ceteras/CoBra/adapter/s-video/images/20240106_163255.jpg

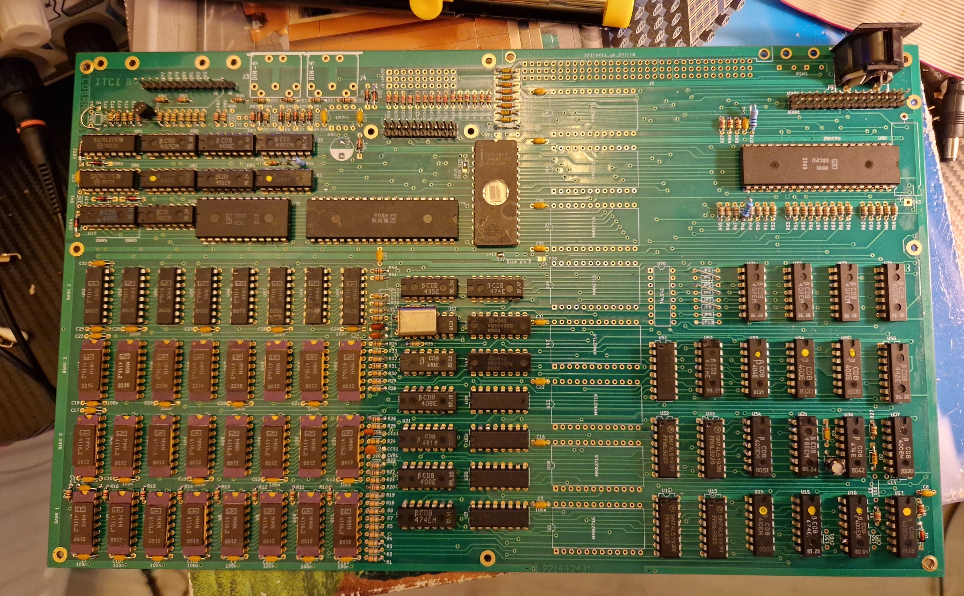
adapter/s-video/images/20240106_163255.jpg
