ceteras/CoBra/adapter/USB-Keyboard/images/20240617_141832.jpg

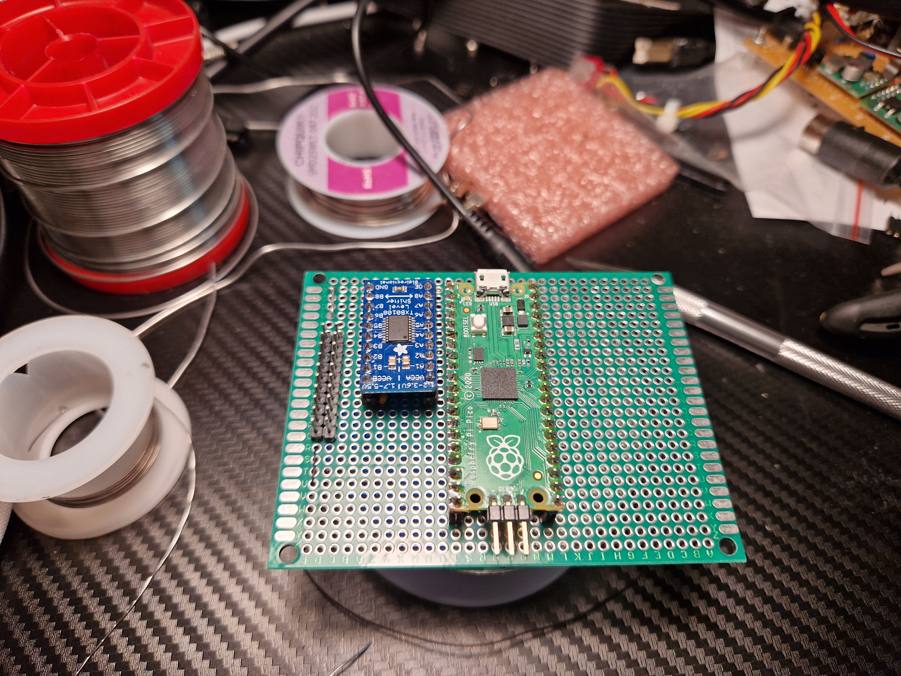
adapter/USB-Keyboard/images/20240617_141832.jpg
