ceteras/CoBra/mainboard/2layer/kicad/main.png

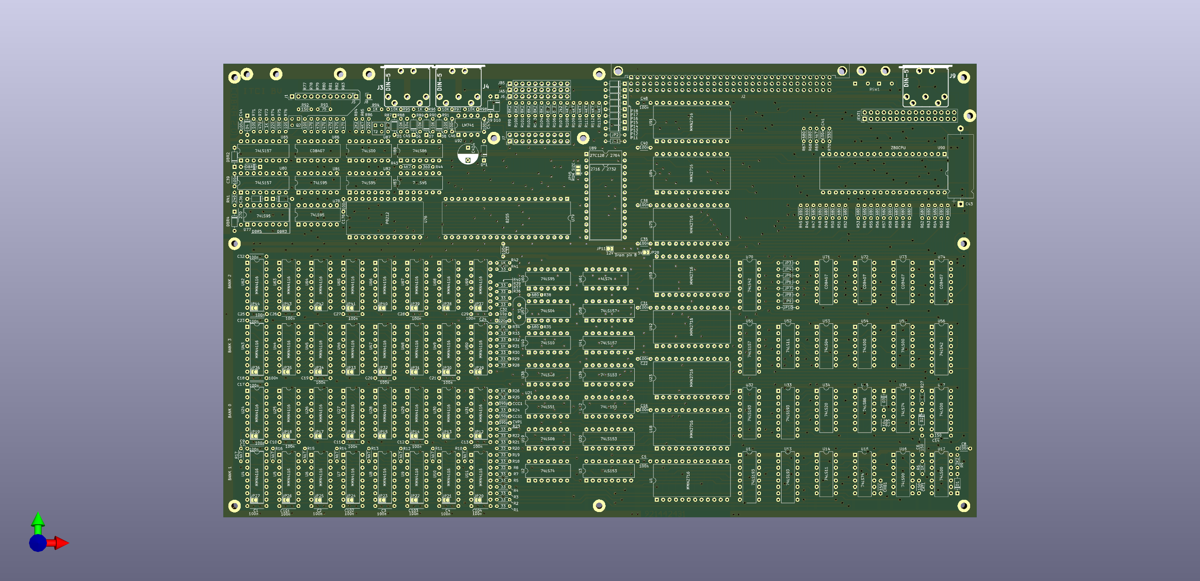
mainboard/2layer/kicad/main.png
