ceteras/CoBra/mainboard/2layer/kicad/Interface.kicad_sch

## KiCad design mainboard/2layer/kicad/Interface.kicad_sch (2023-11-16)

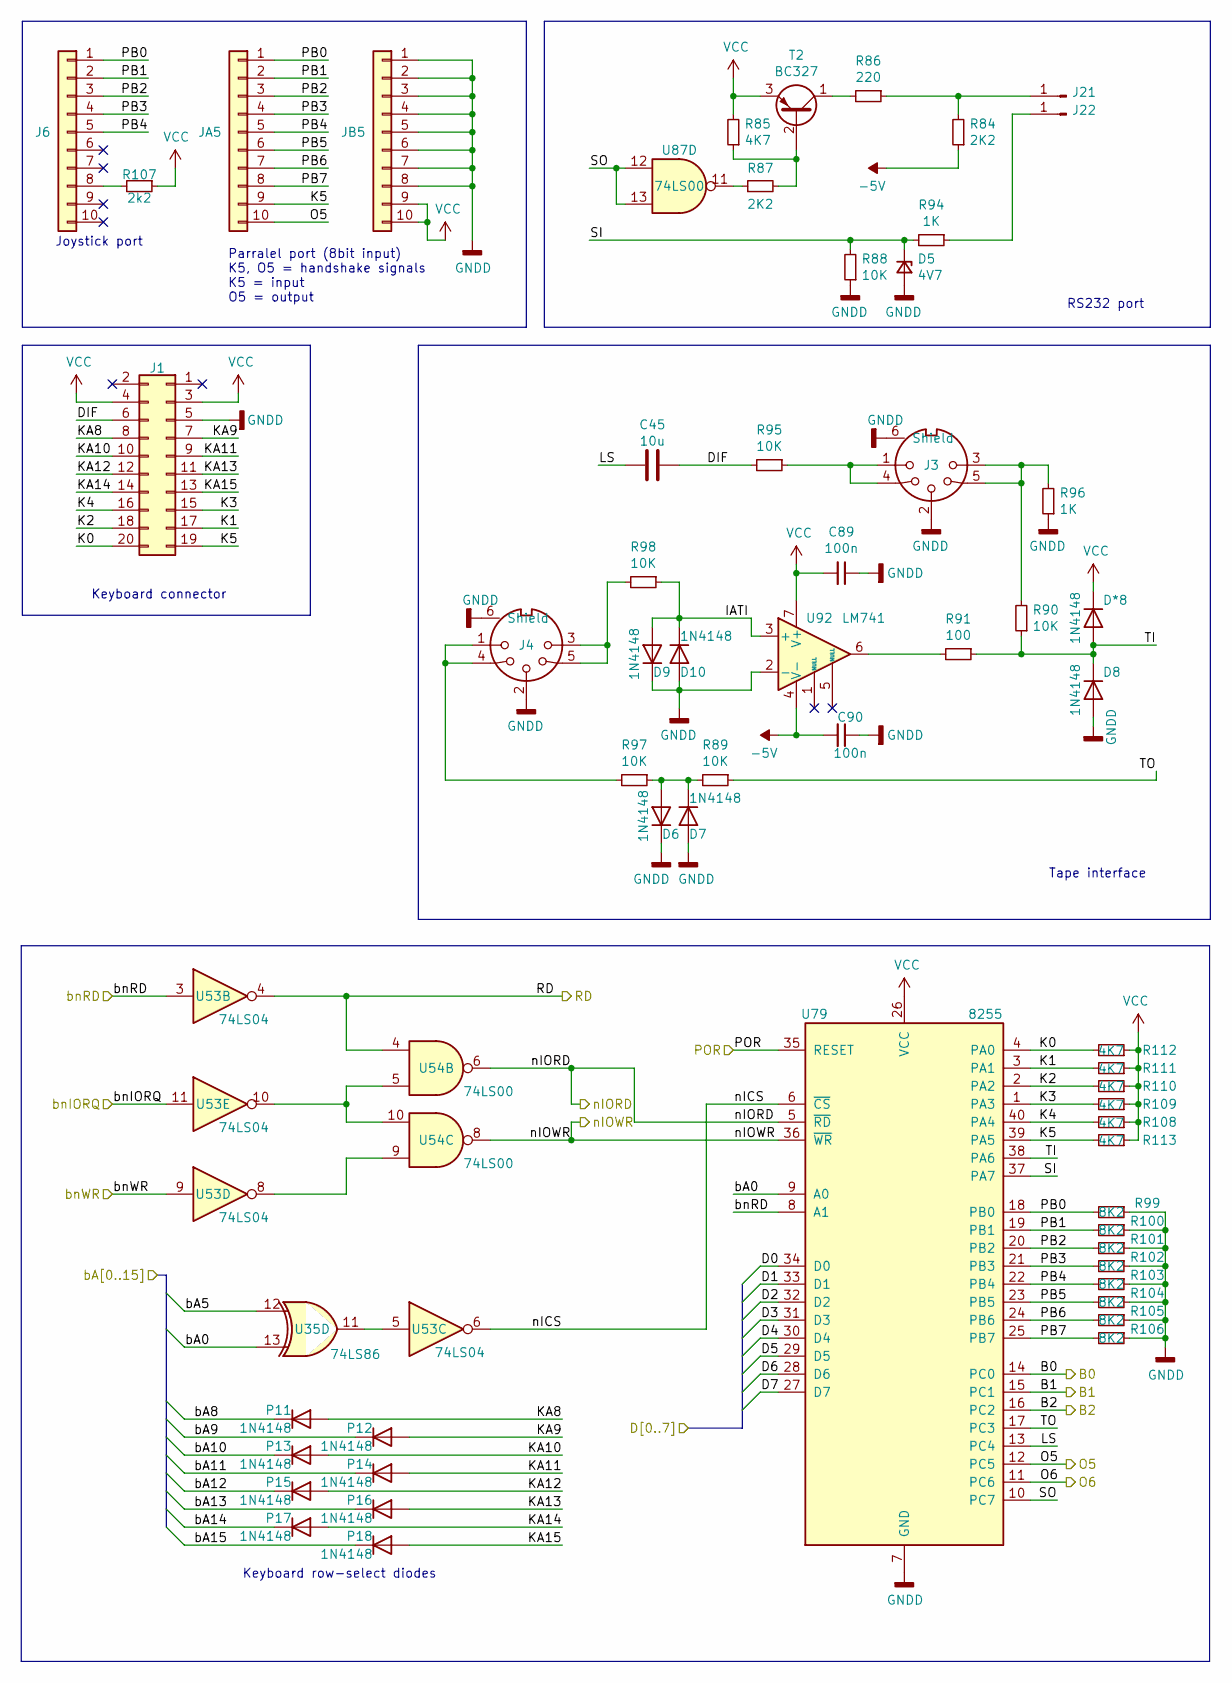
[picture p32: schematic Interface.kicad_sch]

Parts:
C45: 10u; C_THT_508_254
C89, C90: 100n; C_THT_508_254
D5: 4V7; D_DO-35_SOD27_P7.62mm_Horizontal
D6, D7, D8, D9, D10: 1N4148; D_DO-35_SOD27_P7.62mm_Horizontal
D*8: 1N4148; D_DO-35_SOD27_P7.62mm_Horizontal
J1: Conn_02x10_Odd_Even_MountingPin; PinHeader_2x10_P2.54mm_Vertical
J3, J4: DIN-5
J6: Conn_01x10; PinHeader_1x10_P2.54mm_Vertical
J21, J22: Conn_01x01_Male; PinHeader_1x01_P2.54mm_Vertical
JA5: Conn_01x10; PinHeader_1x10_P2.54mm_Vertical
JB5: Conn_01x10; PinHeader_1x10_P2.54mm_Vertical
P11, P12, P13, P14, P15, P16, P17, P18: 1N4148; D_DO-35_SOD27_P7.62mm_Horizontal
R84, R87: 2K2; R_Axial_DIN0204_L3.6mm_D1.6mm_P5.08mm_Horizontal
R85, R108, R109, R110, R111, R112, R113: 4K7; R_Axial_DIN0204_L3.6mm_D1.6mm_P5.08mm_Horizontal
R86: 220; R_Axial_DIN0204_L3.6mm_D1.6mm_P5.08mm_Horizontal
R88, R89, R90, R95, R97, R98: 10K; R_Axial_DIN0204_L3.6mm_D1.6mm_P5.08mm_Horizontal
R91: 100; R_Axial_DIN0204_L3.6mm_D1.6mm_P5.08mm_Horizontal
R94, R96: 1K; R_Axial_DIN0204_L3.6mm_D1.6mm_P5.08mm_Horizontal
R99, R100, R101, R102, R103, R104, R105, R106: 8K2; R_Axial_DIN0204_L3.6mm_D1.6mm_P5.08mm_Horizontal
R107: 2k2; R_Axial_DIN0204_L3.6mm_D1.6mm_P5.08mm_Horizontal
T2: BC327; TO-92-CobraRev
U35: 74LS86; DIP-14_W7.62mm
U53: 74LS04; DIP-14_W7.62mm
U54, U87: 74LS00; DIP-14_W7.62mm
U79: 8255; DIP-40_W15.24mm
U92: LM741; DIP-8_W7.62mm

Connections:
-5V: C90.2, R84.1, U92.4 (V-)
B0: U79.14 (PC0)
B1: U79.15 (PC1)
B2: U79.16 (PC2)
D0: U79.34 (D0)
D1: U79.33 (D1)
D2: U79.32 (D2)
D3: U79.31 (D3)
D4: U79.30 (D4)
D5: U79.29 (D5)
D6: U79.28 (D6)
D7: U79.27 (D7)
DIF: C45.2, J1.6, R95.2
GNDD: C89.1, C90.1, D5.2 (A), D6.1 (K), D7.2 (A), D8.2 (A), D9.1 (K), D10.2 (A), J1.5, J3.2, J3.6 (Shield), J4.2, J4.6 (Shield), JB5.1, JB5.2, JB5.3, JB5.4, JB5.5, JB5.6, JB5.7, JB5.8, R88.1, R96.1, R99.1, R100.1, R101.1, R102.1, R103.1, R104.1, R105.1, R106.1, U79.7 (GND), U92.2 (-)
IATI: D9.2 (A), D10.1 (K), R98.1, U92.3 (+)
K0: J1.20, R112.2, U79.4 (PA0)
K1: J1.17, R111.2, U79.3 (PA1)
K2: J1.18, R110.2, U79.2 (PA2)
K3: J1.15, R109.2, U79.1 (PA3)
K4: J1.16, R108.2, U79.40 (PA4)
K5: J1.19, JA5.9, R113.2, U79.39 (PA5)
KA8: J1.8, P11.2 (A)
KA9: J1.7, P12.2 (A)
KA10: J1.10, P13.2 (A)
KA11: J1.9, P14.2 (A)
KA12: J1.12, P15.2 (A)
KA13: J1.11, P16.2 (A)
KA14: J1.14, P17.2 (A)
KA15: J1.13, P18.2 (A)
LS: C45.1, U79.13 (PC4)
unnamed: D6.2 (A), D7.1 (K), R89.2, R97.1
unnamed: J3.1, J3.4, R95.1
unnamed: J3.3, J3.5, R90.2, R96.2
unnamed: J4.1, J4.4, R97.2
unnamed: J4.3, J4.5, R98.2
unnamed: J6.8, R107.2
unnamed: J21.1, R84.2, R86.1
unnamed: J22.1, R94.1
unnamed: R85.1, R87.2, T2.2 (B)
unnamed: R86.2, T2.1 (C)
unnamed: R87.1, U87.11
unnamed: R91.2, U92.6
unnamed: U35.11, U53.5
unnamed: U53.8, U54.9
unnamed: U53.10, U54.5, U54.10
O5: JA5.10, U79.12 (PC5)
O6: U79.11 (PC6)
PB0: J6.1, JA5.1, R99.2, U79.18 (PB0)
PB1: J6.2, JA5.2, R100.2, U79.19 (PB1)
PB2: J6.3, JA5.3, R101.2, U79.20 (PB2)
PB3: J6.4, JA5.4, R102.2, U79.21 (PB3)
PB4: J6.5, JA5.5, R103.2, U79.22 (PB4)
PB5: JA5.6, R104.2, U79.23 (PB5)
PB6: JA5.7, R105.2, U79.24 (PB6)
PB7: JA5.8, R106.2, U79.25 (PB7)
POR: U79.35 (RESET)
RD: U53.4, U54.4
SI: D5.1 (K), R88.2, R94.2, U79.37 (PA7)
SO: U79.10 (PC7), U87.12, U87.13
TI: D8.1 (K), D*8.2 (A), R90.1, R91.1, U79.38 (PA6)
TO: R89.1, U79.17 (PC3)
VCC: C89.2, D*8.1 (K), J1.3, J1.4, JB5.9, JB5.10, R85.2, R107.1, R108.1, R109.1, R110.1, R111.1, R112.1, R113.1, T2.3 (E), U79.26 (VCC), U92.7 (V+)
bA0: U35.13, U79.9 (A0)
bA5: U35.12
bA8: P11.1 (K)
bA9: P12.1 (K)
bA10: P13.1 (K)
bA11: P14.1 (K)
bA12: P15.1 (K)
bA13: P16.1 (K)
bA14: P17.1 (K)
bA15: P18.1 (K)
bnIORQ: U53.11
bnRD: U53.3, U79.8 (A1)
bnWR: U53.9
nICS: U53.6, U79.6 (~CS)
nIORD: U54.6, U79.5 (~RD)
nIOWR: U54.8, U79.36 (~WR)

Notes on the sheet:
Tape interface
Keyboard connector
Keyboard row-select diodes
Joystick port
RS232 port
Parralel port (8bit input) K5, O5 = handshake signals K5 = input O5 = output
