ceteras/CoBra/mainboard/2layer/kicad/Memory_arbiter_cmd.kicad_sch

## KiCad design mainboard/2layer/kicad/Memory_arbiter_cmd.kicad_sch (2023-11-17)

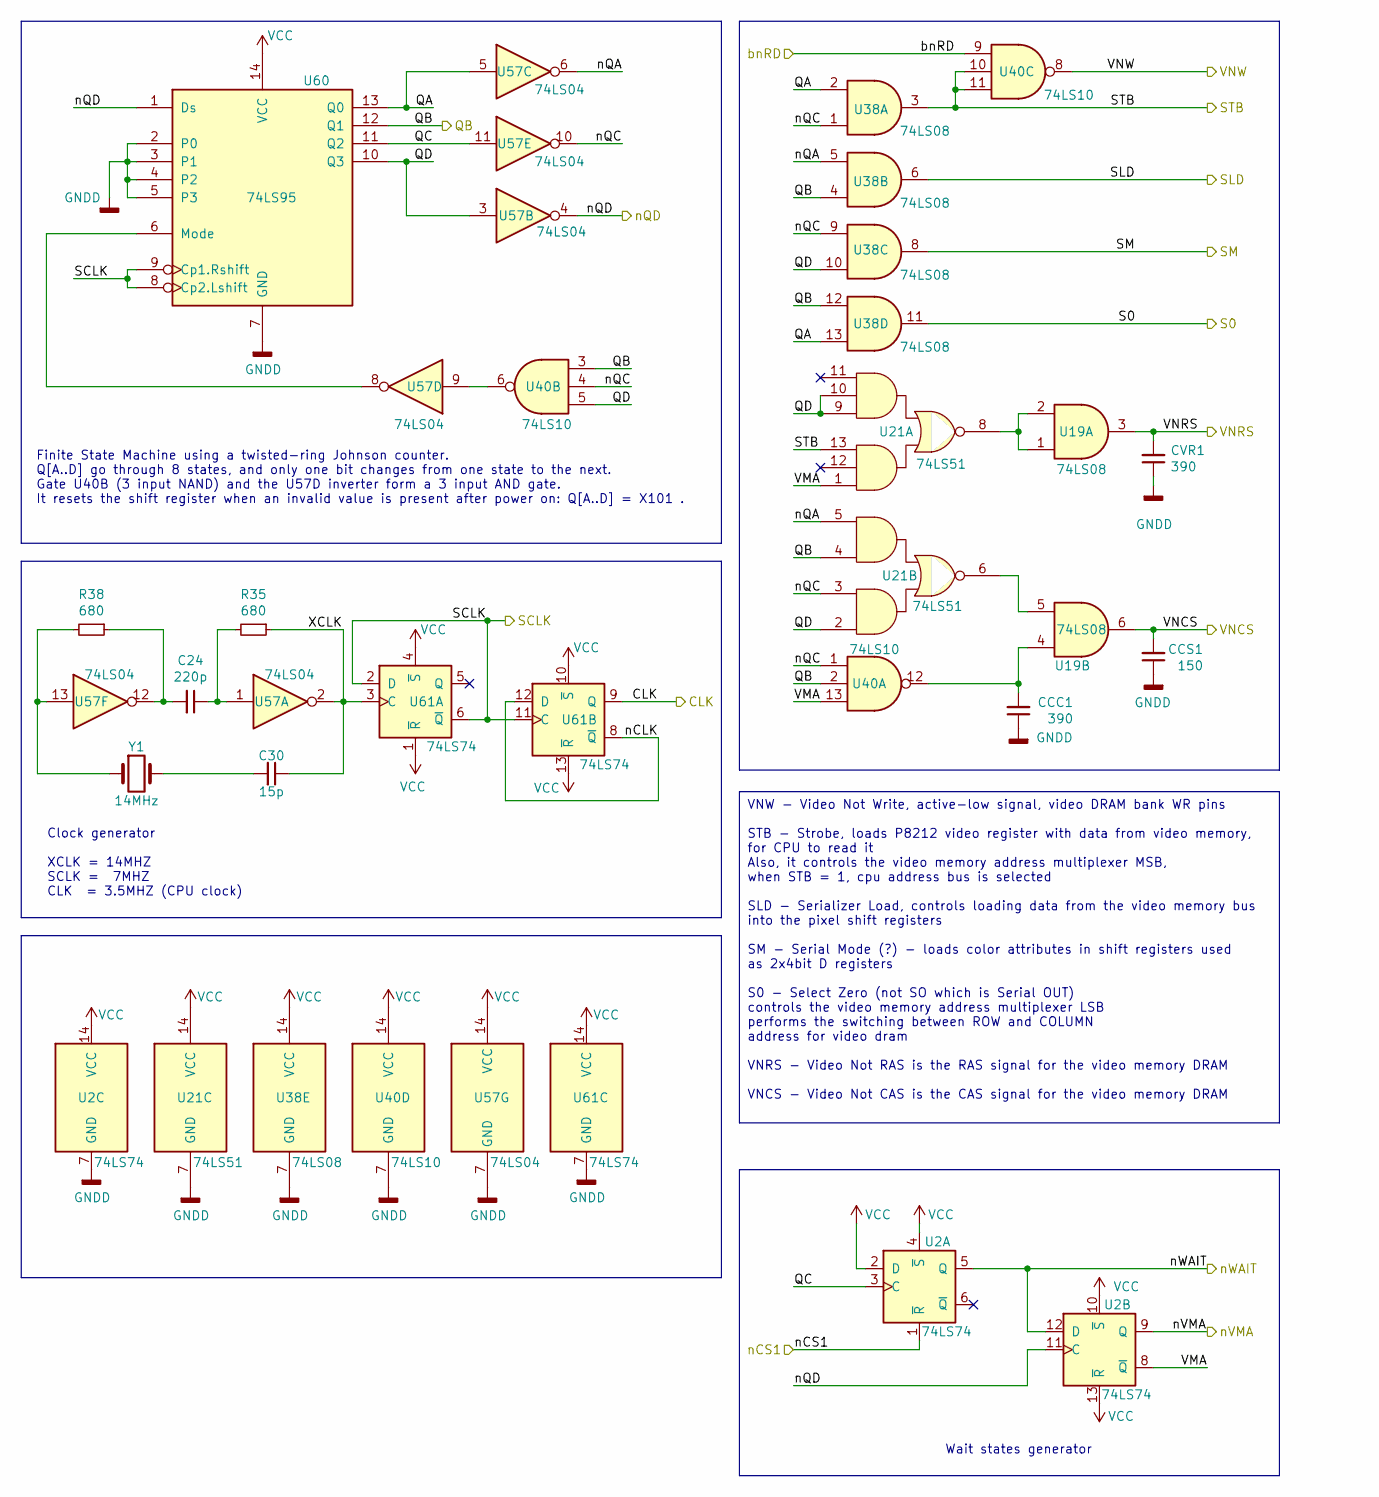
[picture p33: schematic Memory_arbiter_cmd.kicad_sch]

Parts:
C24: 220p; C_THT_508_254
C30: 15p; C_THT_508_254
CCC1: 390; C_THT_508_254
CCS1: 150; C_THT_508_254
CVR1: 390; C_THT_508_254
R35, R38: 680; R_Axial_DIN0204_L3.6mm_D1.6mm_P5.08mm_Horizontal
U2, U61: 74LS74; DIP-14_W7.62mm
U19, U38: 74LS08; DIP-14_W7.62mm
U21: 74LS51; DIP-14_W7.62mm
U40: 74LS10; DIP-14_W7.62mm
U57: 74LS04; DIP-14_W7.62mm
U60: 74LS95; DIP-14_W7.62mm
Y1: 14MHz; Crystal_HC18-U_Vertical

Connections:
CLK: U61.9 (Q)
GNDD: CCC1.1, CCS1.1, CVR1.1, U2.7 (GND), U21.7 (GND), U38.7 (GND), U40.7 (GND), U57.7 (GND), U60.2 (P0), U60.3 (P1), U60.4 (P2), U60.5 (P3), U60.7 (GND), U61.7 (GND)
unnamed: C24.1, R35.2, U57.1
unnamed: C24.2, R38.1, U57.12
unnamed: C30.2, Y1.2
unnamed: CCC1.2, U19.4, U40.12
unnamed: R38.2, U57.13, Y1.1
unnamed: U19.1, U19.2, U21.8
unnamed: U19.5, U21.6
unnamed: U40.6, U57.9
unnamed: U57.8, U60.6 (Mode)
QA: U38.2, U38.13, U57.5, U60.13 (Q0)
QB: U21.4, U38.4, U38.12, U40.2, U40.3, U60.12 (Q1)
QC: U2.3 (C), U57.11, U60.11 (Q2)
QD: U21.2, U21.9, U21.10, U38.10, U40.5, U57.3, U60.10 (Q3)
S0: U38.11
SCLK: U60.8 (Cp2.Lshift), U60.9 (Cp1.Rshift), U61.2 (D), U61.6 (~Q), U61.11 (C)
SLD: U38.6
SM: U38.8
STB: U21.13, U38.3, U40.10, U40.11
VCC: U2.2 (D), U2.4 (~S), U2.10 (~S), U2.13 (~R), U2.14 (VCC), U21.14 (VCC), U38.14 (VCC), U40.14 (VCC), U57.14 (VCC), U60.14 (VCC), U61.1 (~R), U61.4 (~S), U61.10 (~S), U61.13 (~R), U61.14 (VCC)
VMA: U2.8 (~Q), U21.1, U40.13
VNCS: CCS1.2, U19.6
VNRS: CVR1.2, U19.3
VNW: U40.8
XCLK: C30.1, R35.1, U57.2, U61.3 (C)
bnRD: U40.9
nCLK: U61.8 (~Q), U61.12 (D)
nCS1: U2.1 (~R)
nQA: U21.5, U38.5, U57.6
nQC: U21.3, U38.1, U38.9, U40.1, U40.4, U57.10
nQD: U2.11 (C), U57.4, U60.1 (Ds)
nVMA: U2.9 (Q)
nWAIT: U2.5 (Q), U2.12 (D)

Notes on the sheet:
VNW - Video Not Write, active-low signal, video DRAM bank WR pins STB - Strobe, loads P8212 video register with data from video memory, for CPU to read it Also, it controls the video memory address multiplexer MSB, when STB = 1, cpu address bus is selected SLD - Serializer Load, controls loading da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
Wait states generator
Clock generator XCLK = 14MHZ SCLK = 7MHZ CLK = 3.5MHZ (CPU clock)
Finite State Machine using a twisted-ring Johnson counter. Q[A..D] go through 8 states, and only one bit changes from one state to the next. Gate U40B (3 input NAND) and the U57D inverter form a 3 input AND gate. It resets the shift register when an invalid value is present after power on: Q[A..D] 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
