ceteras/CoBra/mainboard/2layer/kicad/Mux_video_address.kicad_sch

## KiCad design mainboard/2layer/kicad/Mux_video_address.kicad_sch (2023-11-15)

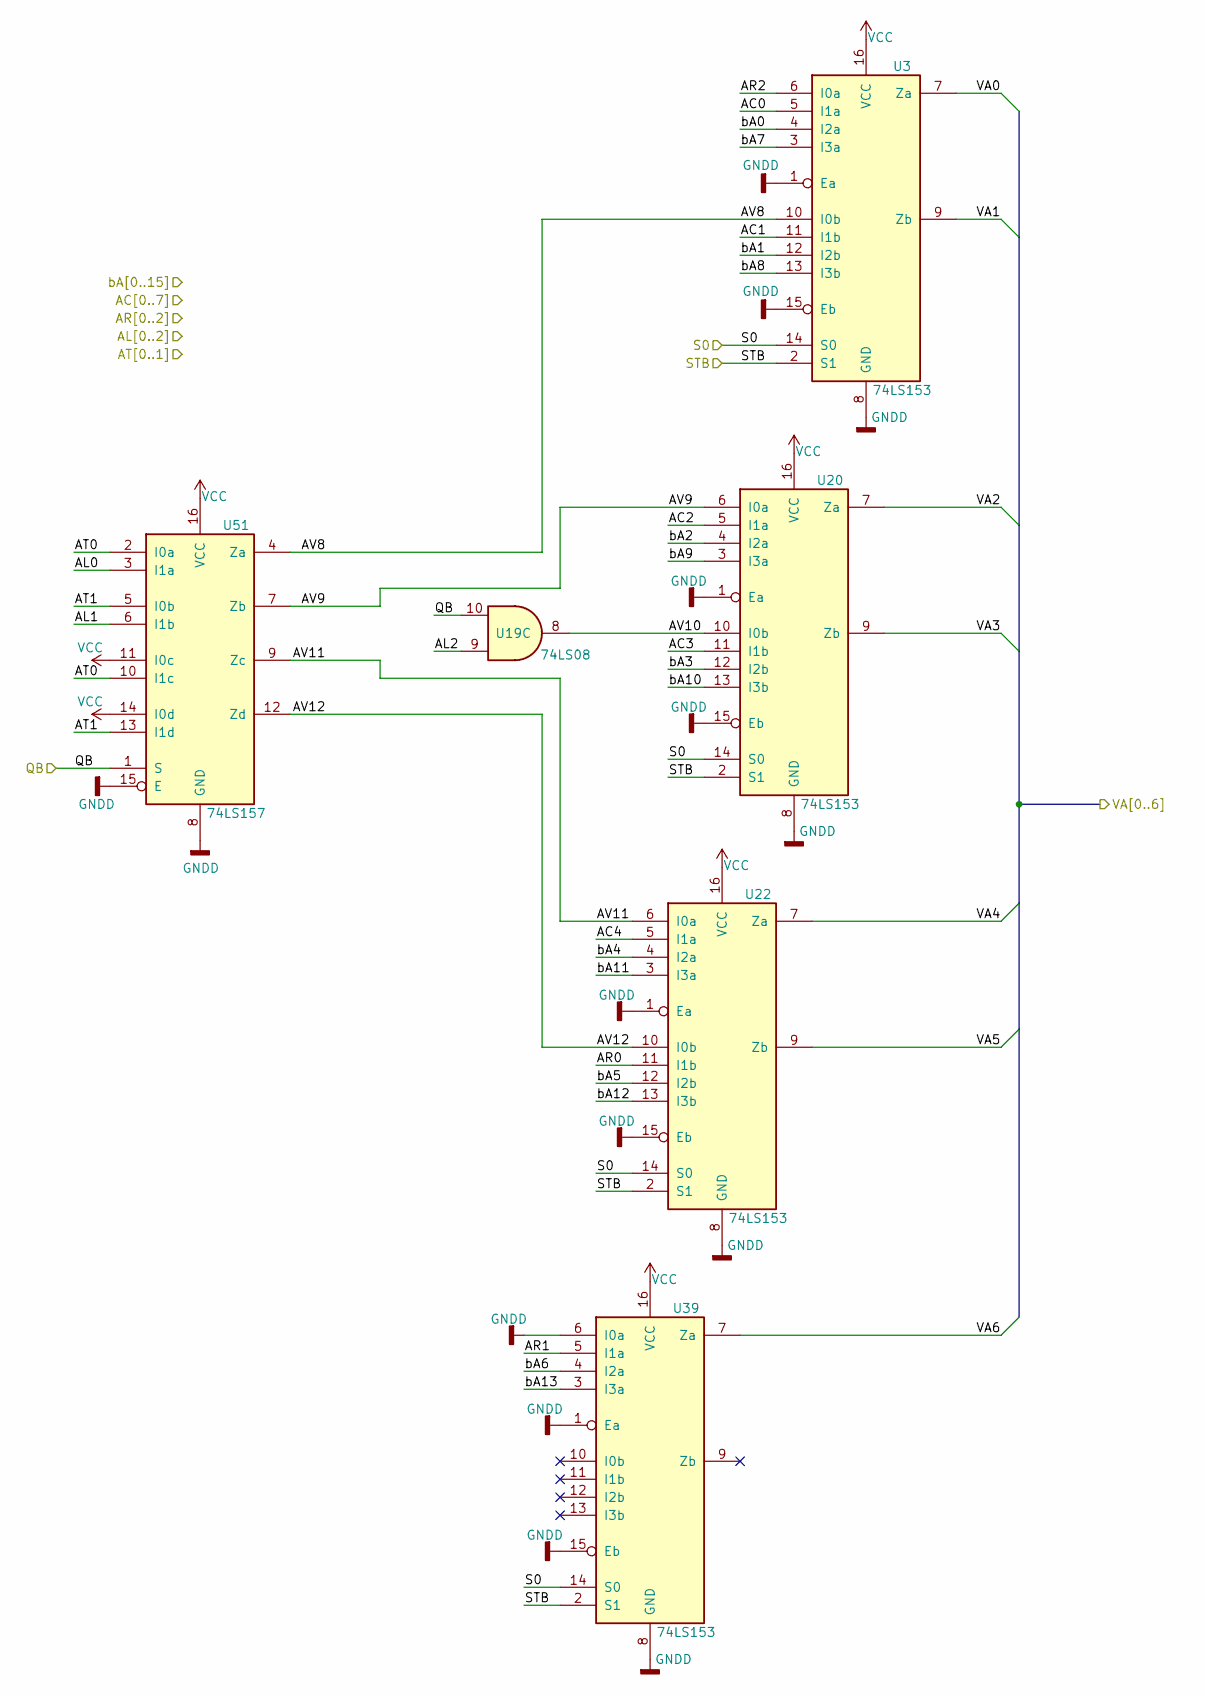
[picture p34: schematic Mux_video_address.kicad_sch]

Parts:
U3, U20, U22, U39: 74LS153; DIP-16_W7.62mm
U19: 74LS08; DIP-14_W7.62mm
U51: 74LS157; DIP-16_W7.62mm

Connections:
AC0: U3.5 (I1a)
AC1: U3.11 (I1b)
AC2: U20.5 (I1a)
AC3: U20.11 (I1b)
AC4: U22.5 (I1a)
AL0: U51.3 (I1a)
AL1: U51.6 (I1b)
AL2: U19.9
AR0: U22.11 (I1b)
AR1: U39.5 (I1a)
AR2: U3.6 (I0a)
AT0: U51.2 (I0a), U51.10 (I1c)
AT1: U51.5 (I0b), U51.13 (I1d)
AV8: U3.10 (I0b), U51.4 (Za)
AV9: U20.6 (I0a), U51.7 (Zb)
AV10: U19.8, U20.10 (I0b)
AV11: U22.6 (I0a), U51.9 (Zc)
AV12: U22.10 (I0b), U51.12 (Zd)
GNDD: U3.1 (Ea), U3.8 (GND), U3.15 (Eb), U20.1 (Ea), U20.8 (GND), U20.15 (Eb), U22.1 (Ea), U22.8 (GND), U22.15 (Eb), U39.1 (Ea), U39.6 (I0a), U39.8 (GND), U39.15 (Eb), U51.8 (GND), U51.15 (E)
QB: U19.10, U51.1 (S)
S0: U3.14 (S0), U20.14 (S0), U22.14 (S0), U39.14 (S0)
STB: U3.2 (S1), U20.2 (S1), U22.2 (S1), U39.2 (S1)
VA0: U3.7 (Za)
VA1: U3.9 (Zb)
VA2: U20.7 (Za)
VA3: U20.9 (Zb)
VA4: U22.7 (Za)
VA5: U22.9 (Zb)
VA6: U39.7 (Za)
VCC: U3.16 (VCC), U20.16 (VCC), U22.16 (VCC), U39.16 (VCC), U51.11 (I0c), U51.14 (I0d), U51.16 (VCC)
bA0: U3.4 (I2a)
bA1: U3.12 (I2b)
bA2: U20.4 (I2a)
bA3: U20.12 (I2b)
bA4: U22.4 (I2a)
bA5: U22.12 (I2b)
bA6: U39.4 (I2a)
bA7: U3.3 (I3a)
bA8: U3.13 (I3b)
bA9: U20.3 (I3a)
bA10: U20.13 (I3b)
bA11: U22.3 (I3a)
bA12: U22.13 (I3b)
bA13: U39.3 (I3a)
