ceteras/CoBra/mainboard/2layer/kicad/RAM_48.kicad_sch

## KiCad design mainboard/2layer/kicad/RAM_48.kicad_sch (2023-11-16)

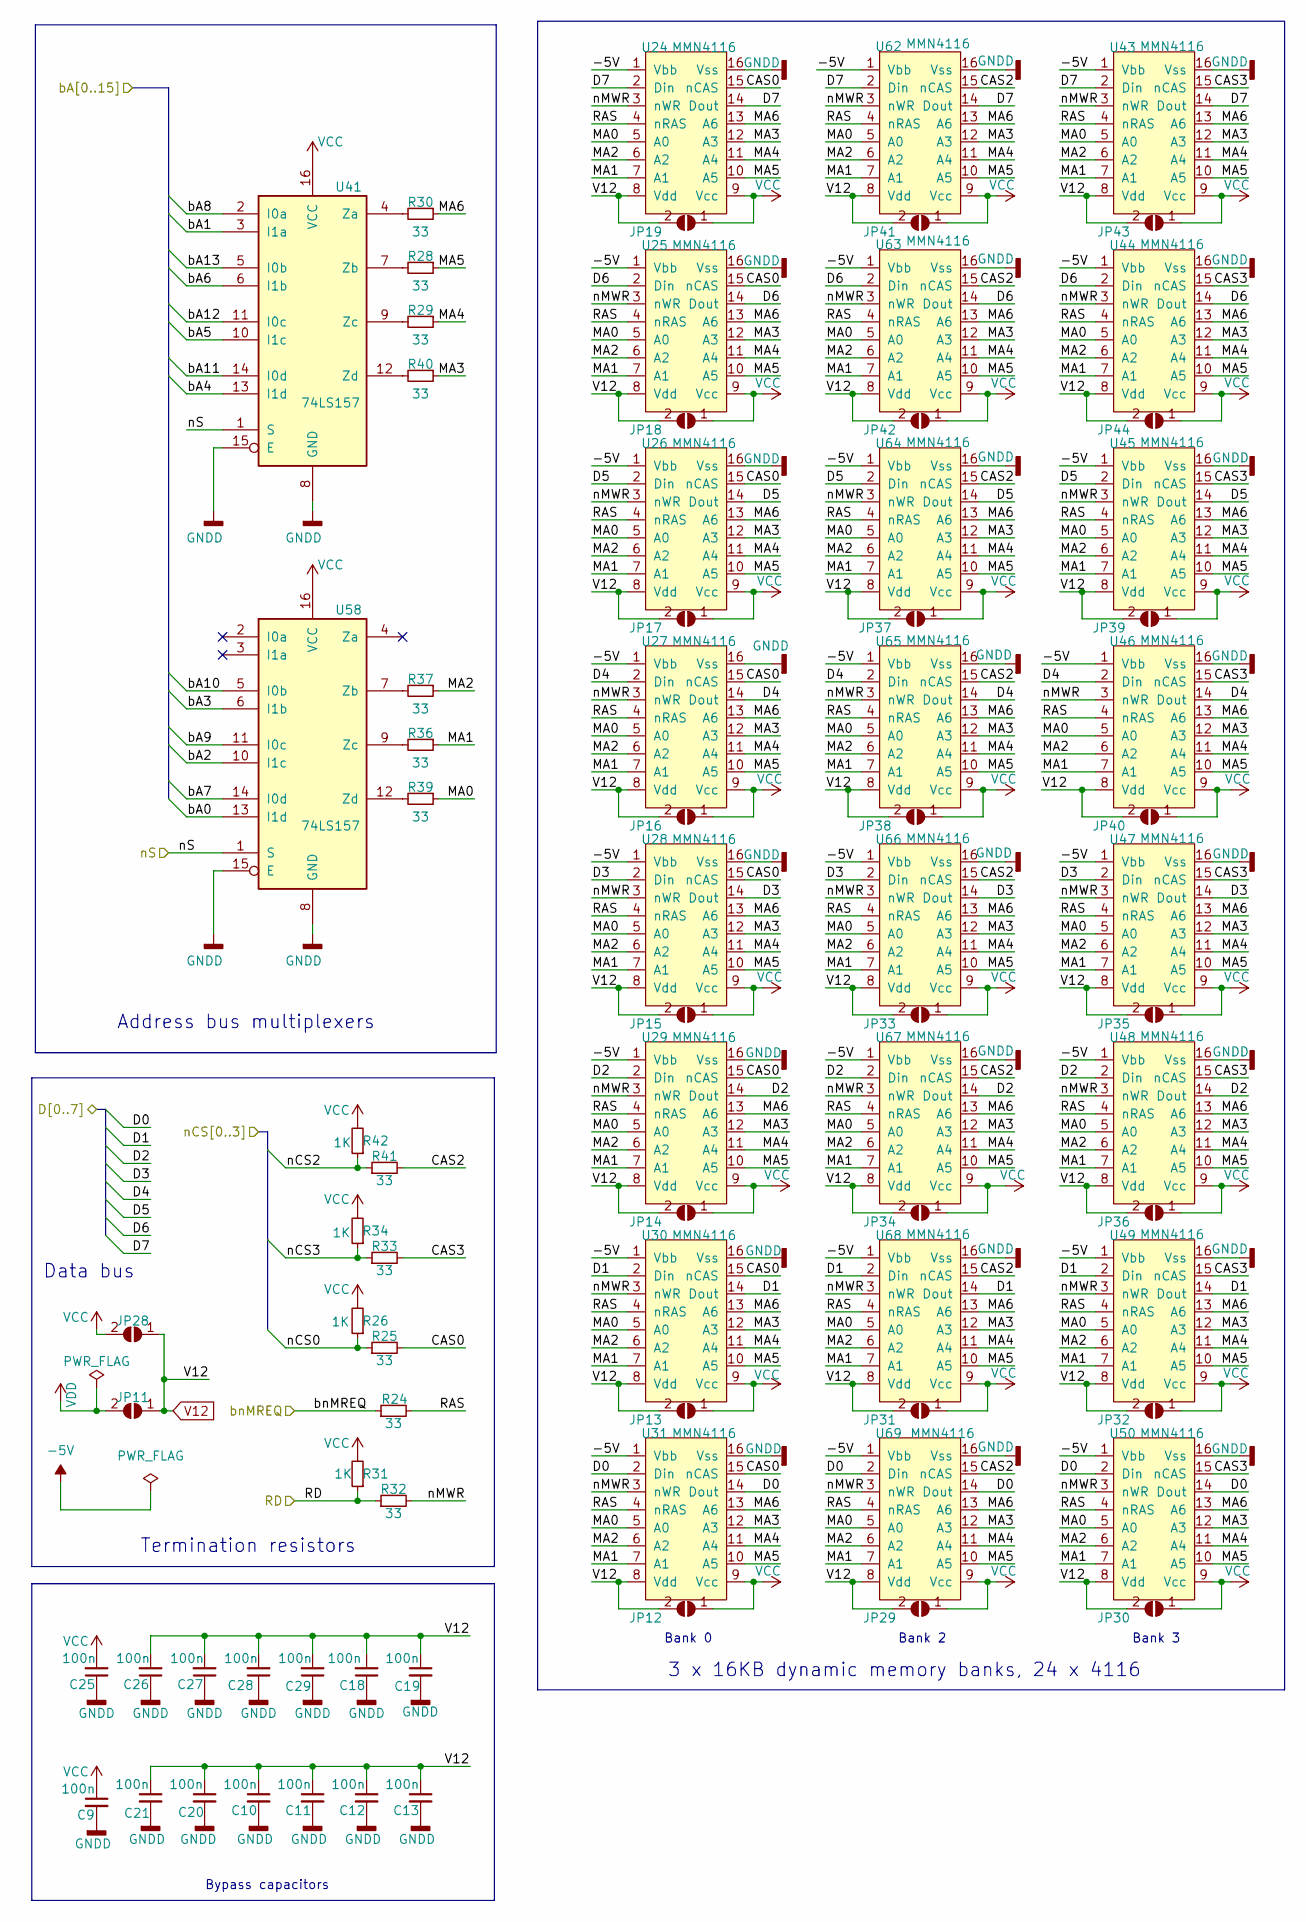
[picture p35: schematic RAM_48.kicad_sch]

Parts:
C9, C10, C11, C12, C13, C18, C19, C20, C21, C25, C26, C27, C28, C29: 100n; C_THT_762_254
JP11, JP12, JP13, JP14, JP15, JP16, JP17, JP18, JP19, JP28, JP29, JP30, JP31, JP32, JP33, JP34, JP35, JP36, JP37, JP38, JP39, JP40, JP41, JP42, JP43, JP44: SolderJumper_2_Open; SolderJumper-2_P1.3mm_Open_TrianglePad1.0x1.5mm
R24, R25, R28, R29, R30, R32, R33, R36, R37, R39, R40, R41: 33; R_Axial_DIN0204_L3.6mm_D1.6mm_P5.08mm_Horizontal
R26, R31, R34, R42: 1K; R_Axial_DIN0204_L3.6mm_D1.6mm_P5.08mm_Horizontal
U24, U25, U26, U27, U28, U29, U30, U31, U43, U44, U45, U46, U47, U48, U49, U50, U62, U63, U64, U65, U66, U67, U68, U69: MMN4116; DIP-16_W7.62mm
U41, U58: 74LS157; DIP-16_W7.62mm

Connections:
-5V: U24.1 (Vbb), U25.1 (Vbb), U26.1 (Vbb), U27.1 (Vbb), U28.1 (Vbb), U29.1 (Vbb), U30.1 (Vbb), U31.1 (Vbb), U43.1 (Vbb), U44.1 (Vbb), U45.1 (Vbb), U46.1 (Vbb), U47.1 (Vbb), U48.1 (Vbb), U49.1 (Vbb), U50.1 (Vbb), U62.1 (Vbb), U63.1 (Vbb), U64.1 (Vbb), U65.1 (Vbb), U66.1 (Vbb), U67.1 (Vbb), U68.1 (Vbb), U69.1 (Vbb)
CAS0: R25.2, U24.15 (nCAS), U25.15 (nCAS), U26.15 (nCAS), U27.15 (nCAS), U28.15 (nCAS), U29.15 (nCAS), U30.15 (nCAS), U31.15 (nCAS)
CAS2: R41.2, U62.15 (nCAS), U63.15 (nCAS), U64.15 (nCAS), U65.15 (nCAS), U66.15 (nCAS), U67.15 (nCAS), U68.15 (nCAS), U69.15 (nCAS)
CAS3: R33.2, U43.15 (nCAS), U44.15 (nCAS), U45.15 (nCAS), U46.15 (nCAS), U47.15 (nCAS), U48.15 (nCAS), U49.15 (nCAS), U50.15 (nCAS)
D0: U31.2 (Din), U31.14 (Dout), U50.2 (Din), U50.14 (Dout), U69.2 (Din), U69.14 (Dout)
D1: U30.2 (Din), U30.14 (Dout), U49.2 (Din), U49.14 (Dout), U68.2 (Din), U68.14 (Dout)
D2: U29.2 (Din), U29.14 (Dout), U48.2 (Din), U48.14 (Dout), U67.2 (Din), U67.14 (Dout)
D3: U28.2 (Din), U28.14 (Dout), U47.2 (Din), U47.14 (Dout), U66.2 (Din), U66.14 (Dout)
D4: U27.2 (Din), U27.14 (Dout), U46.2 (Din), U46.14 (Dout), U65.2 (Din), U65.14 (Dout)
D5: U26.2 (Din), U26.14 (Dout), U45.2 (Din), U45.14 (Dout), U64.2 (Din), U64.14 (Dout)
D6: U25.2 (Din), U25.14 (Dout), U44.2 (Din), U44.14 (Dout), U63.2 (Din), U63.14 (Dout)
D7: U24.2 (Din), U24.14 (Dout), U43.2 (Din), U43.14 (Dout), U62.2 (Din), U62.14 (Dout)
GNDD: C9.2, C10.2, C11.2, C12.2, C13.2, C18.1, C19.2, C20.2, C21.2, C25.1, C26.1, C27.1, C28.1, C29.1, U24.16 (Vss), U25.16 (Vss), U26.16 (Vss), U27.16 (Vss), U28.16 (Vss), U29.16 (Vss), U30.16 (Vss), U31.16 (Vss), U41.8 (GND), U41.15 (E), U43.16 (Vss), U44.16 (Vss), U45.16 (Vss), U46.16 (Vss), U47.16 (Vss), U48.16 (Vss), U49.16 (Vss), U50.16 (Vss), U58.8 (GND), U58.15 (E), U62.16 (Vss), U63.16 (Vss), U64.16 (Vss), U65.16 (Vss), U66.16 (Vss), U67.16 (Vss), U68.16 (Vss), U69.16 (Vss)
MA0: R39.1, U24.5 (A0), U25.5 (A0), U26.5 (A0), U27.5 (A0), U28.5 (A0), U29.5 (A0), U30.5 (A0), U31.5 (A0), U43.5 (A0), U44.5 (A0), U45.5 (A0), U46.5 (A0), U47.5 (A0), U48.5 (A0), U49.5 (A0), U50.5 (A0), U62.5 (A0), U63.5 (A0), U64.5 (A0), U65.5 (A0), U66.5 (A0), U67.5 (A0), U68.5 (A0), U69.5 (A0)
MA1: R36.1, U24.7 (A1), U25.7 (A1), U26.7 (A1), U27.7 (A1), U28.7 (A1), U29.7 (A1), U30.7 (A1), U31.7 (A1), U43.7 (A1), U44.7 (A1), U45.7 (A1), U46.7 (A1), U47.7 (A1), U48.7 (A1), U49.7 (A1), U50.7 (A1), U62.7 (A1), U63.7 (A1), U64.7 (A1), U65.7 (A1), U66.7 (A1), U67.7 (A1), U68.7 (A1), U69.7 (A1)
MA2: R37.1, U24.6 (A2), U25.6 (A2), U26.6 (A2), U27.6 (A2), U28.6 (A2), U29.6 (A2), U30.6 (A2), U31.6 (A2), U43.6 (A2), U44.6 (A2), U45.6 (A2), U46.6 (A2), U47.6 (A2), U48.6 (A2), U49.6 (A2), U50.6 (A2), U62.6 (A2), U63.6 (A2), U64.6 (A2), U65.6 (A2), U66.6 (A2), U67.6 (A2), U68.6 (A2), U69.6 (A2)
MA3: R40.1, U24.12 (A3), U25.12 (A3), U26.12 (A3), U27.12 (A3), U28.12 (A3), U29.12 (A3), U30.12 (A3), U31.12 (A3), U43.12 (A3), U44.12 (A3), U45.12 (A3), U46.12 (A3), U47.12 (A3), U48.12 (A3), U49.12 (A3), U50.12 (A3), U62.12 (A3), U63.12 (A3), U64.12 (A3), U65.12 (A3), U66.12 (A3), U67.12 (A3), U68.12 (A3), U69.12 (A3)
MA4: R29.1, U24.11 (A4), U25.11 (A4), U26.11 (A4), U27.11 (A4), U28.11 (A4), U29.11 (A4), U30.11 (A4), U31.11 (A4), U43.11 (A4), U44.11 (A4), U45.11 (A4), U46.11 (A4), U47.11 (A4), U48.11 (A4), U49.11 (A4), U50.11 (A4), U62.11 (A4), U63.11 (A4), U64.11 (A4), U65.11 (A4), U66.11 (A4), U67.11 (A4), U68.11 (A4), U69.11 (A4)
MA5: R28.1, U24.10 (A5), U25.10 (A5), U26.10 (A5), U27.10 (A5), U28.10 (A5), U29.10 (A5), U30.10 (A5), U31.10 (A5), U43.10 (A5), U44.10 (A5), U45.10 (A5), U46.10 (A5), U47.10 (A5), U48.10 (A5), U49.10 (A5), U50.10 (A5), U62.10 (A5), U63.10 (A5), U64.10 (A5), U65.10 (A5), U66.10 (A5), U67.10 (A5), U68.10 (A5), U69.10 (A5)
MA6: R30.1, U24.13 (A6), U25.13 (A6), U26.13 (A6), U27.13 (A6), U28.13 (A6), U29.13 (A6), U30.13 (A6), U31.13 (A6), U43.13 (A6), U44.13 (A6), U45.13 (A6), U46.13 (A6), U47.13 (A6), U48.13 (A6), U49.13 (A6), U50.13 (A6), U62.13 (A6), U63.13 (A6), U64.13 (A6), U65.13 (A6), U66.13 (A6), U67.13 (A6), U68.13 (A6), U69.13 (A6)
unnamed: R28.2, U41.7 (Zb)
unnamed: R29.2, U41.9 (Zc)
unnamed: R30.2, U41.4 (Za)
unnamed: R36.2, U58.9 (Zc)
unnamed: R37.2, U58.7 (Zb)
unnamed: R39.2, U58.12 (Zd)
unnamed: R40.2, U41.12 (Zd)
RAS: R24.2, U24.4 (nRAS), U25.4 (nRAS), U26.4 (nRAS), U27.4 (nRAS), U28.4 (nRAS), U29.4 (nRAS), U30.4 (nRAS), U31.4 (nRAS), U43.4 (nRAS), U44.4 (nRAS), U45.4 (nRAS), U46.4 (nRAS), U47.4 (nRAS), U48.4 (nRAS), U49.4 (nRAS), U50.4 (nRAS), U62.4 (nRAS), U63.4 (nRAS), U64.4 (nRAS), U65.4 (nRAS), U66.4 (nRAS), U67.4 (nRAS), U68.4 (nRAS), U69.4 (nRAS)
RD: R31.1, R32.1
V12: C10.1, C11.1, C12.1, C13.1, C18.2, C19.1, C20.1, C21.1, C26.2, C27.2, C28.2, C29.2, JP11.1 (A), JP12.2 (B), JP13.2 (B), JP14.2 (B), JP15.2 (B), JP16.2 (B), JP17.2 (B), JP18.2 (B), JP19.2 (B), JP28.1 (A), JP29.2 (B), JP30.2 (B), JP31.2 (B), JP32.2 (B), JP33.2 (B), JP34.2 (B), JP35.2 (B), JP36.2 (B), JP37.2 (B), JP38.2 (B), JP39.2 (B), JP40.2 (B), JP41.2 (B), JP42.2 (B), JP43.2 (B), JP44.2 (B), U24.8 (Vdd), U25.8 (Vdd), U26.8 (Vdd), U27.8 (Vdd), U28.8 (Vdd), U29.8 (Vdd), U30.8 (Vdd), U31.8 (Vdd), U43.8 (Vdd), U44.8 (Vdd), U45.8 (Vdd), U46.8 (Vdd), U47.8 (Vdd), U48.8 (Vdd), U49.8 (Vdd), U50.8 (Vdd), U62.8 (Vdd), U63.8 (Vdd), U64.8 (Vdd), U65.8 (Vdd), U66.8 (Vdd), U67.8 (Vdd), U68.8 (Vdd), U69.8 (Vdd)
VCC: C9.1, C25.2, JP12.1 (A), JP13.1 (A), JP14.1 (A), JP15.1 (A), JP16.1 (A), JP17.1 (A), JP18.1 (A), JP19.1 (A), JP28.2 (B), JP29.1 (A), JP30.1 (A), JP31.1 (A), JP32.1 (A), JP33.1 (A), JP34.1 (A), JP35.1 (A), JP36.1 (A), JP37.1 (A), JP38.1 (A), JP39.1 (A), JP40.1 (A), JP41.1 (A), JP42.1 (A), JP43.1 (A), JP44.1 (A), R26.2, R31.2, R34.2, R42.2, U24.9 (Vcc), U25.9 (Vcc), U26.9 (Vcc), U27.9 (Vcc), U28.9 (Vcc), U29.9 (Vcc), U30.9 (Vcc), U31.9 (Vcc), U41.16 (VCC), U43.9 (Vcc), U44.9 (Vcc), U45.9 (Vcc), U46.9 (Vcc), U47.9 (Vcc), U48.9 (Vcc), U49.9 (Vcc), U50.9 (Vcc), U58.16 (VCC), U62.9 (Vcc), U63.9 (Vcc), U64.9 (Vcc), U65.9 (Vcc), U66.9 (Vcc), U67.9 (Vcc), U68.9 (Vcc), U69.9 (Vcc)
VDD: JP11.2 (B)
bA0: U58.13 (I1d)
bA1: U41.3 (I1a)
bA2: U58.10 (I1c)
bA3: U58.6 (I1b)
bA4: U41.13 (I1d)
bA5: U41.10 (I1c)
bA6: U41.6 (I1b)
bA7: U58.14 (I0d)
bA8: U41.2 (I0a)
bA9: U58.11 (I0c)
bA10: U58.5 (I0b)
bA11: U41.14 (I0d)
bA12: U41.11 (I0c)
bA13: U41.5 (I0b)
bnMREQ: R24.1
nCS0: R25.1, R26.1
nCS2: R41.1, R42.1
nCS3: R33.1, R34.1
nMWR: R32.2, U24.3 (nWR), U25.3 (nWR), U26.3 (nWR), U27.3 (nWR), U28.3 (nWR), U29.3 (nWR), U30.3 (nWR), U31.3 (nWR), U43.3 (nWR), U44.3 (nWR), U45.3 (nWR), U46.3 (nWR), U47.3 (nWR), U48.3 (nWR), U49.3 (nWR), U50.3 (nWR), U62.3 (nWR), U63.3 (nWR), U64.3 (nWR), U65.3 (nWR), U66.3 (nWR), U67.3 (nWR), U68.3 (nWR), U69.3 (nWR)
nS: U41.1 (S), U58.1 (S)

Notes on the sheet:
Bank 2
Bypass capacitors
Data bus
Address bus multiplexers
Bank 3
3 x 16KB dynamic memory banks, 24 x 4116
Bank 0
Termination resistors
