ceteras/CoBra/mainboard/2layer/kicad/ROM.kicad_sch

## KiCad design mainboard/2layer/kicad/ROM.kicad_sch (2024-06-28)

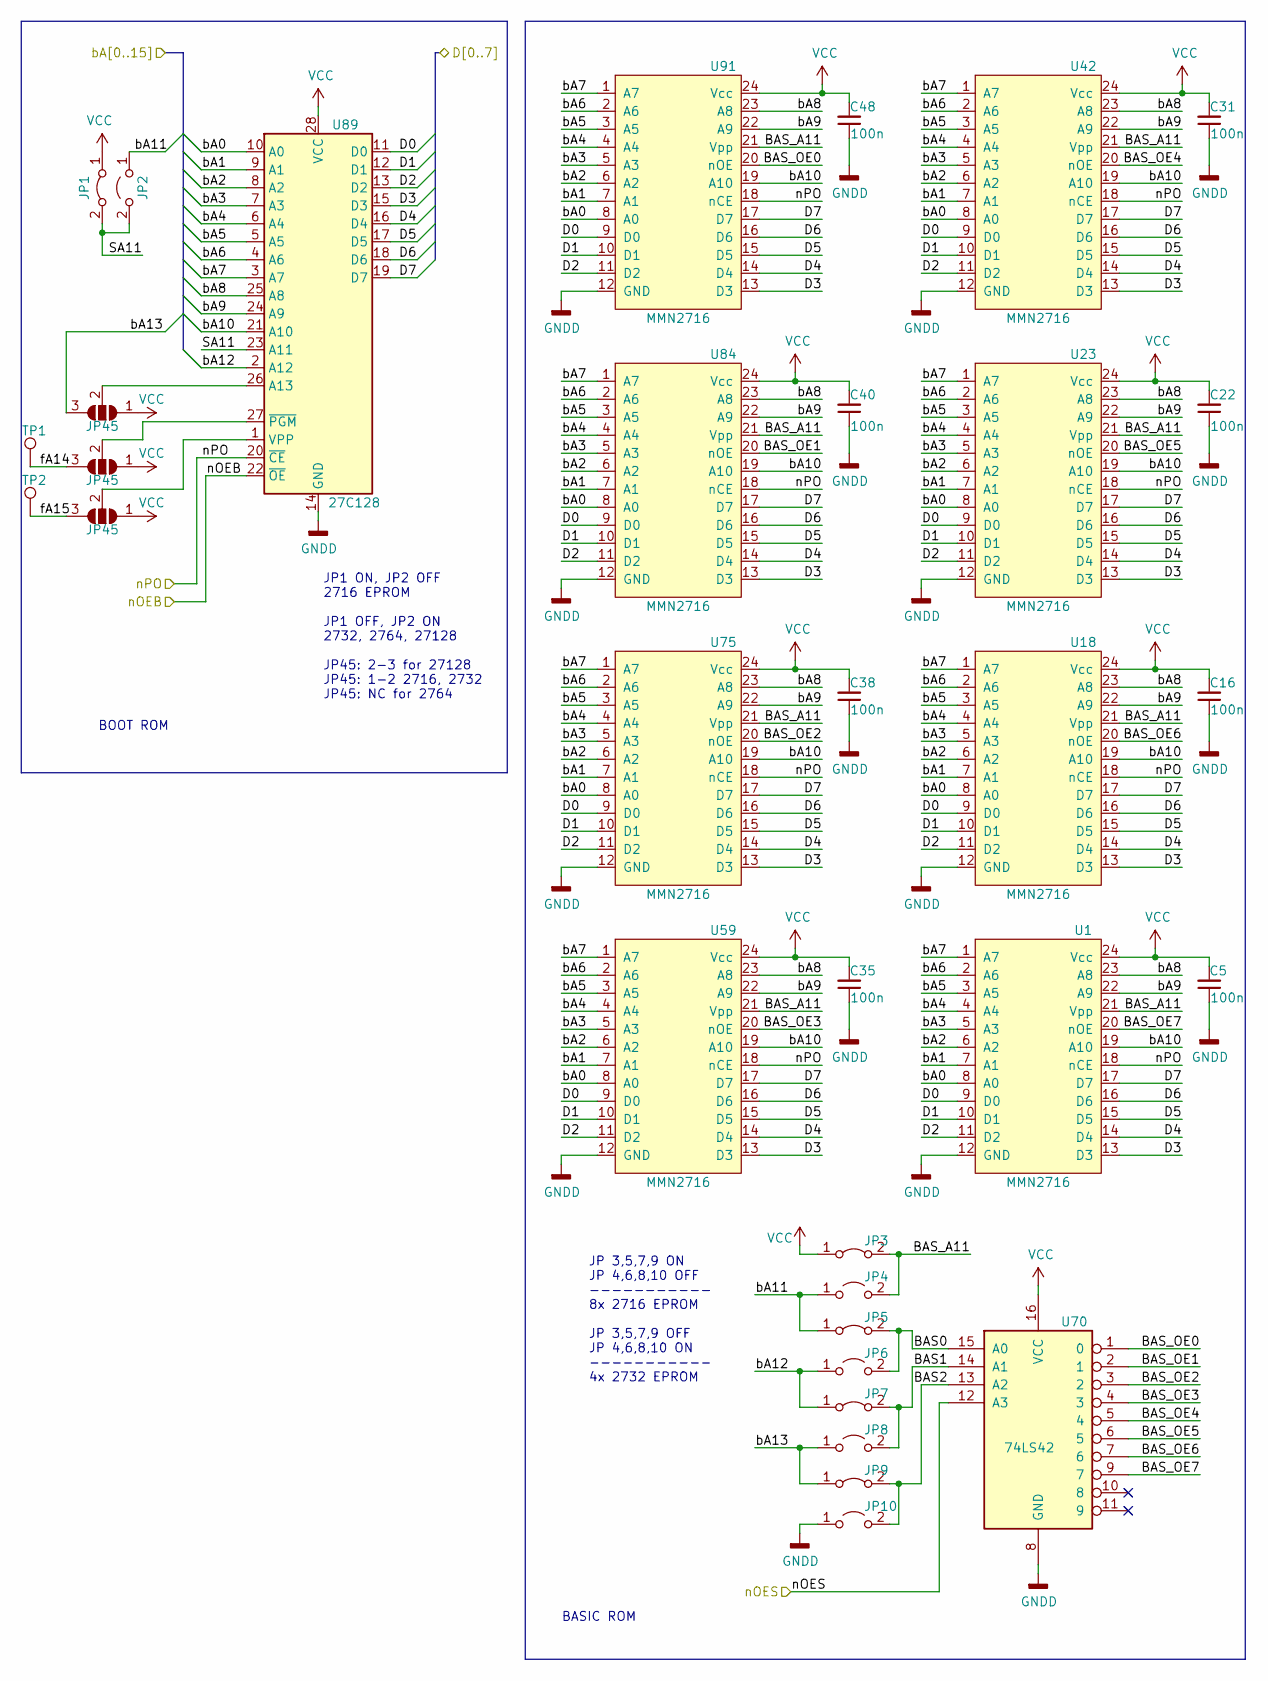
[picture p36: schematic ROM.kicad_sch]

Parts:
C5, C16, C22, C31, C35, C38, C40, C48: 100n; C_THT_508_254
JP1, JP3, JP5, JP7, JP9: Jumper_NC_Small; R_Axial_DIN0204_L3.6mm_D1.6mm_P7.62mm_Horizontal
JP2, JP4, JP6, JP8, JP10: Jumper_NO_Small; R_Axial_DIN0204_L3.6mm_D1.6mm_P7.62mm_Horizontal
JP45: SolderJumper_3_Open; SolderJumper-3_P1.3mm_Open_Pad1.0x1.5mm
TP1, TP2: TestPoint_THTPad_1.5x1.5mm_Drill0.7mm
U1, U18, U23, U42, U59, U75, U84, U91: MMN2716; DIP-24_W15.24mm
U70: 74LS42; DIP-16_W7.62mm
U89: 27C128; DIP-28_W15.24mm

Connections:
BAS0: JP5.2 (B), JP6.2 (B), U70.15 (A0)
BAS1: JP7.2 (B), JP8.2 (B), U70.14 (A1)
BAS2: JP9.2 (B), JP10.2 (B), U70.13 (A2)
BAS_A11: JP3.2 (B), JP4.2 (B), U1.21 (Vpp), U18.21 (Vpp), U23.21 (Vpp), U42.21 (Vpp), U59.21 (Vpp), U75.21 (Vpp), U84.21 (Vpp), U91.21 (Vpp)
BAS_OE0: U70.1 (0), U91.20 (nOE)
BAS_OE1: U70.2 (1), U84.20 (nOE)
BAS_OE2: U70.3 (2), U75.20 (nOE)
BAS_OE3: U59.20 (nOE), U70.4 (3)
BAS_OE4: U42.20 (nOE), U70.5 (4)
BAS_OE5: U23.20 (nOE), U70.6 (5)
BAS_OE6: U18.20 (nOE), U70.7 (6)
BAS_OE7: U1.20 (nOE), U70.9 (7)
D0: U1.9 (D0), U18.9 (D0), U23.9 (D0), U42.9 (D0), U59.9 (D0), U75.9 (D0), U84.9 (D0), U89.11 (D0), U91.9 (D0)
D1: U1.10 (D1), U18.10 (D1), U23.10 (D1), U42.10 (D1), U59.10 (D1), U75.10 (D1), U84.10 (D1), U89.12 (D1), U91.10 (D1)
D2: U1.11 (D2), U18.11 (D2), U23.11 (D2), U42.11 (D2), U59.11 (D2), U75.11 (D2), U84.11 (D2), U89.13 (D2), U91.11 (D2)
D3: U1.13 (D3), U18.13 (D3), U23.13 (D3), U42.13 (D3), U59.13 (D3), U75.13 (D3), U84.13 (D3), U89.15 (D3), U91.13 (D3)
D4: U1.14 (D4), U18.14 (D4), U23.14 (D4), U42.14 (D4), U59.14 (D4), U75.14 (D4), U84.14 (D4), U89.16 (D4), U91.14 (D4)
D5: U1.15 (D5), U18.15 (D5), U23.15 (D5), U42.15 (D5), U59.15 (D5), U75.15 (D5), U84.15 (D5), U89.17 (D5), U91.15 (D5)
D6: U1.16 (D6), U18.16 (D6), U23.16 (D6), U42.16 (D6), U59.16 (D6), U75.16 (D6), U84.16 (D6), U89.18 (D6), U91.16 (D6)
D7: U1.17 (D7), U18.17 (D7), U23.17 (D7), U42.17 (D7), U59.17 (D7), U75.17 (D7), U84.17 (D7), U89.19 (D7), U91.17 (D7)
GNDD: C5.1, C16.1, C22.1, C31.1, C35.1, C38.1, C40.1, C48.1, JP10.1 (A), U1.12 (GND), U18.12 (GND), U23.12 (GND), U42.12 (GND), U59.12 (GND), U70.8 (GND), U75.12 (GND), U84.12 (GND), U89.14 (GND), U91.12 (GND)
unnamed: JP45.2 (C), U89.1 (VPP), U89.26 (A13), U89.27 (~PGM)
SA11: JP1.2 (B), JP2.2 (B), U89.23 (A11)
VCC: C5.2, C16.2, C22.2, C31.2, C35.2, C38.2, C40.2, C48.2, JP1.1 (A), JP3.1 (A), JP45.1 (A), U1.24 (Vcc), U18.24 (Vcc), U23.24 (Vcc), U42.24 (Vcc), U59.24 (Vcc), U70.16 (VCC), U75.24 (Vcc), U84.24 (Vcc), U89.28 (VCC), U91.24 (Vcc)
bA0: U1.8 (A0), U18.8 (A0), U23.8 (A0), U42.8 (A0), U59.8 (A0), U75.8 (A0), U84.8 (A0), U89.10 (A0), U91.8 (A0)
bA1: U1.7 (A1), U18.7 (A1), U23.7 (A1), U42.7 (A1), U59.7 (A1), U75.7 (A1), U84.7 (A1), U89.9 (A1), U91.7 (A1)
bA2: U1.6 (A2), U18.6 (A2), U23.6 (A2), U42.6 (A2), U59.6 (A2), U75.6 (A2), U84.6 (A2), U89.8 (A2), U91.6 (A2)
bA3: U1.5 (A3), U18.5 (A3), U23.5 (A3), U42.5 (A3), U59.5 (A3), U75.5 (A3), U84.5 (A3), U89.7 (A3), U91.5 (A3)
bA4: U1.4 (A4), U18.4 (A4), U23.4 (A4), U42.4 (A4), U59.4 (A4), U75.4 (A4), U84.4 (A4), U89.6 (A4), U91.4 (A4)
bA5: U1.3 (A5), U18.3 (A5), U23.3 (A5), U42.3 (A5), U59.3 (A5), U75.3 (A5), U84.3 (A5), U89.5 (A5), U91.3 (A5)
bA6: U1.2 (A6), U18.2 (A6), U23.2 (A6), U42.2 (A6), U59.2 (A6), U75.2 (A6), U84.2 (A6), U89.4 (A6), U91.2 (A6)
bA7: U1.1 (A7), U18.1 (A7), U23.1 (A7), U42.1 (A7), U59.1 (A7), U75.1 (A7), U84.1 (A7), U89.3 (A7), U91.1 (A7)
bA8: U1.23 (A8), U18.23 (A8), U23.23 (A8), U42.23 (A8), U59.23 (A8), U75.23 (A8), U84.23 (A8), U89.25 (A8), U91.23 (A8)
bA9: U1.22 (A9), U18.22 (A9), U23.22 (A9), U42.22 (A9), U59.22 (A9), U75.22 (A9), U84.22 (A9), U89.24 (A9), U91.22 (A9)
bA10: U1.19 (A10), U18.19 (A10), U23.19 (A10), U42.19 (A10), U59.19 (A10), U75.19 (A10), U84.19 (A10), U89.21 (A10), U91.19 (A10)
bA11: JP2.1 (A), JP4.1 (A), JP5.1 (A)
bA12: JP6.1 (A), JP7.1 (A), U89.2 (A12)
bA13: JP8.1 (A), JP9.1 (A), JP45.3 (B)
fA14: JP45.3 (B), TP1.1
fA15: JP45.3 (B), TP2.1
nOEB: U89.22 (~OE)
nOES: U70.12 (A3)
nPO: U1.18 (nCE), U18.18 (nCE), U23.18 (nCE), U42.18 (nCE), U59.18 (nCE), U75.18 (nCE), U84.18 (nCE), U89.20 (~CE), U91.18 (nCE)

Notes on the sheet:
JP1 ON, JP2 OFF 2716 EPROM JP1 OFF, JP2 ON 2732, 2764, 27128 JP45: 2-3 for 27128 JP45: 1-2 2716, 2732 JP45: NC for 2764
JP 3,5,7,9 ON JP 4,6,8,10 OFF ----------- 8x 2716 EPROM JP 3,5,7,9 OFF JP 4,6,8,10 ON ----------- 4x 2732 EPROM
BOOT ROM
BASIC ROM
