ceteras/CoBra/mainboard/2layer/kicad/Video_address_gen.kicad_sch

## KiCad design mainboard/2layer/kicad/Video_address_gen.kicad_sch (2023-12-20)

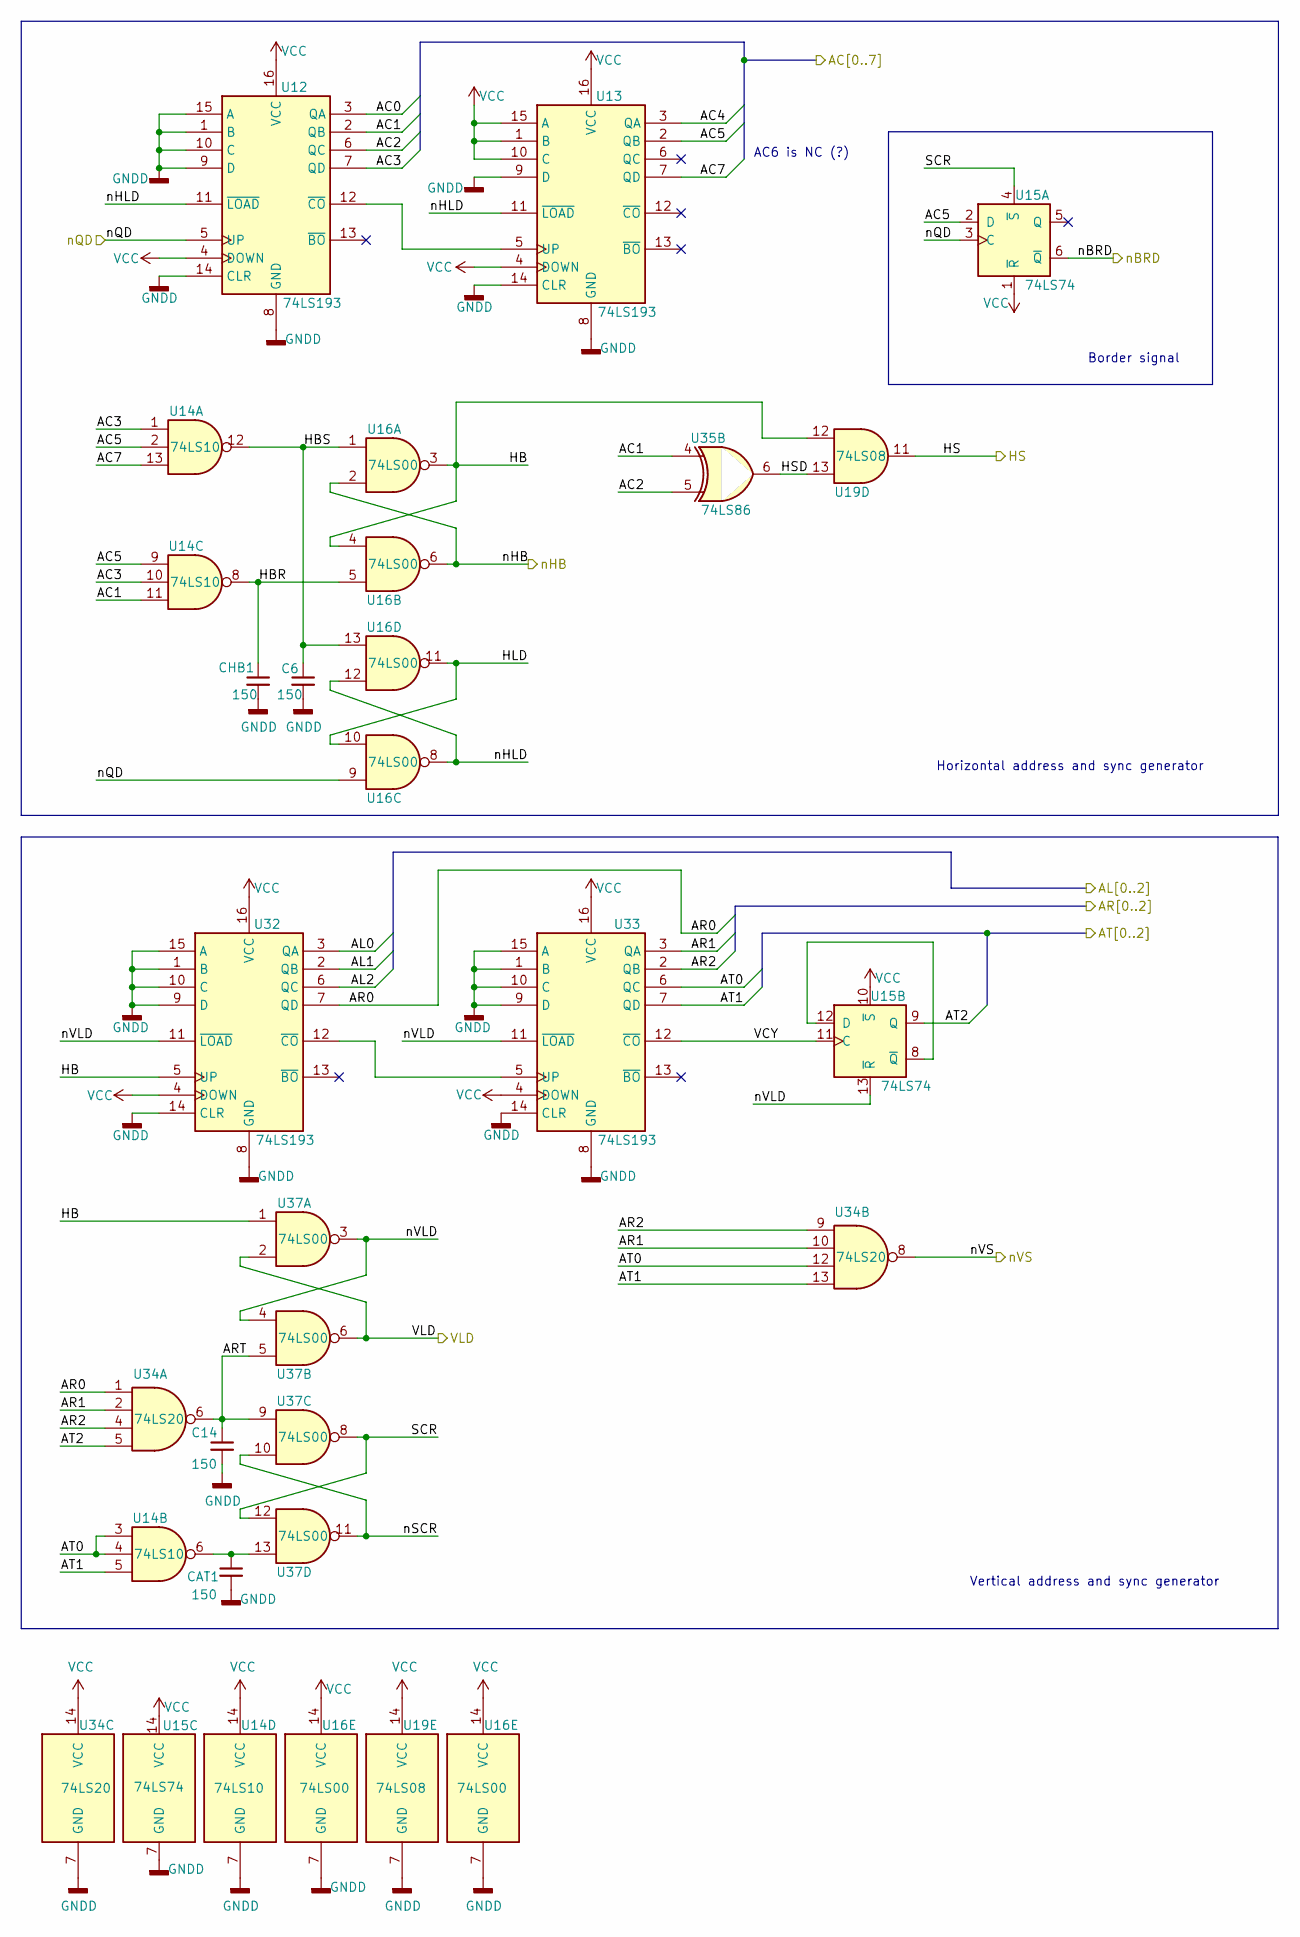
[picture p37: schematic Video_address_gen.kicad_sch]

Parts:
C6, C14: 150; C_THT_762_254
CAT1: 150; C_THT_508_254
CHB1: 150; C_THT_508_254
U12, U13, U32, U33: 74LS193; DIP-16_W7.62mm
U14: 74LS10; DIP-14_W7.62mm
U15: 74LS74; DIP-14_W7.62mm
U16, U37: 74LS00; DIP-14_W7.62mm
U19: 74LS08; DIP-14_W7.62mm
U34: 74LS20; DIP-14_W7.62mm
U35: 74LS86; DIP-14_W7.62mm

Connections:
AC0: U12.3 (QA)
AC1: U12.2 (QB), U14.11, U35.4
AC2: U12.6 (QC), U35.5
AC3: U12.7 (QD), U14.1, U14.10
AC4: U13.3 (QA)
AC5: U13.2 (QB), U14.2, U14.9, U15.2 (D)
AC7: U13.7 (QD), U14.13
AL0: U32.3 (QA)
AL1: U32.2 (QB)
AL2: U32.6 (QC)
AR0: U32.7 (QD), U34.1
AR1: U33.3 (QA), U34.2, U34.10
AR2: U33.2 (QB), U34.4, U34.9
ART: C14.1, U34.6, U37.5, U37.9
AT0: U14.3, U14.4, U33.6 (QC), U34.12
AT1: U14.5, U33.7 (QD), U34.13
AT2: U15.9 (Q), U34.5
GNDD: C6.2, C14.2, CAT1.2, CHB1.2, U12.1 (B), U12.8 (GND), U12.9 (D), U12.10 (C), U12.14 (CLR), U12.15 (A), U13.8 (GND), U13.9 (D), U13.14 (CLR), U14.7 (GND), U15.7 (GND), U16.7 (GND), U19.7 (GND), U32.1 (B), U32.8 (GND), U32.9 (D), U32.10 (C), U32.14 (CLR), U32.15 (A), U33.1 (B), U33.8 (GND), U33.9 (D), U33.10 (C), U33.14 (CLR), U33.15 (A), U34.7 (GND)
HB: U16.3, U16.4, U19.12, U32.5 (UP), U37.1
HBR: CHB1.1, U14.8, U16.5
HBS: C6.1, U14.12, U16.1, U16.13
HLD: U16.10, U16.11
HS: U19.11
HSD: U19.13, U35.6
unnamed: CAT1.1, U14.6, U37.13
unnamed: U12.12 (~CO), U13.5 (UP)
unnamed: U15.8 (~Q), U15.12 (D)
unnamed: U32.12 (~CO), U33.5 (UP)
SCR: U15.4 (~S), U37.8, U37.12
VCC: U12.4 (DOWN), U12.16 (VCC), U13.1 (B), U13.4 (DOWN), U13.10 (C), U13.15 (A), U13.16 (VCC), U14.14 (VCC), U15.1 (~R), U15.10 (~S), U15.14 (VCC), U16.14 (VCC), U19.14 (VCC), U32.4 (DOWN), U32.16 (VCC), U33.4 (DOWN), U33.16 (VCC), U34.14 (VCC)
VCY: U15.11 (C), U33.12 (~CO)
VLD: U37.2, U37.6
nBRD: U15.6 (~Q)
nHB: U16.2, U16.6
nHLD: U12.11 (~LOAD), U13.11 (~LOAD), U16.8, U16.12
nQD: U12.5 (UP), U15.3 (C), U16.9
nSCR: U37.10, U37.11
nVLD: U15.13 (~R), U32.11 (~LOAD), U33.11 (~LOAD), U37.3, U37.4
nVS: U34.8

Notes on the sheet:
Vertical address and sync generator
Horizontal address and sync generator
AC6 is NC (?)
Border signal
