ceteras/CoBra/mainboard/2layer/kicad/Video_memory.kicad_sch

## KiCad design mainboard/2layer/kicad/Video_memory.kicad_sch (2023-11-16)

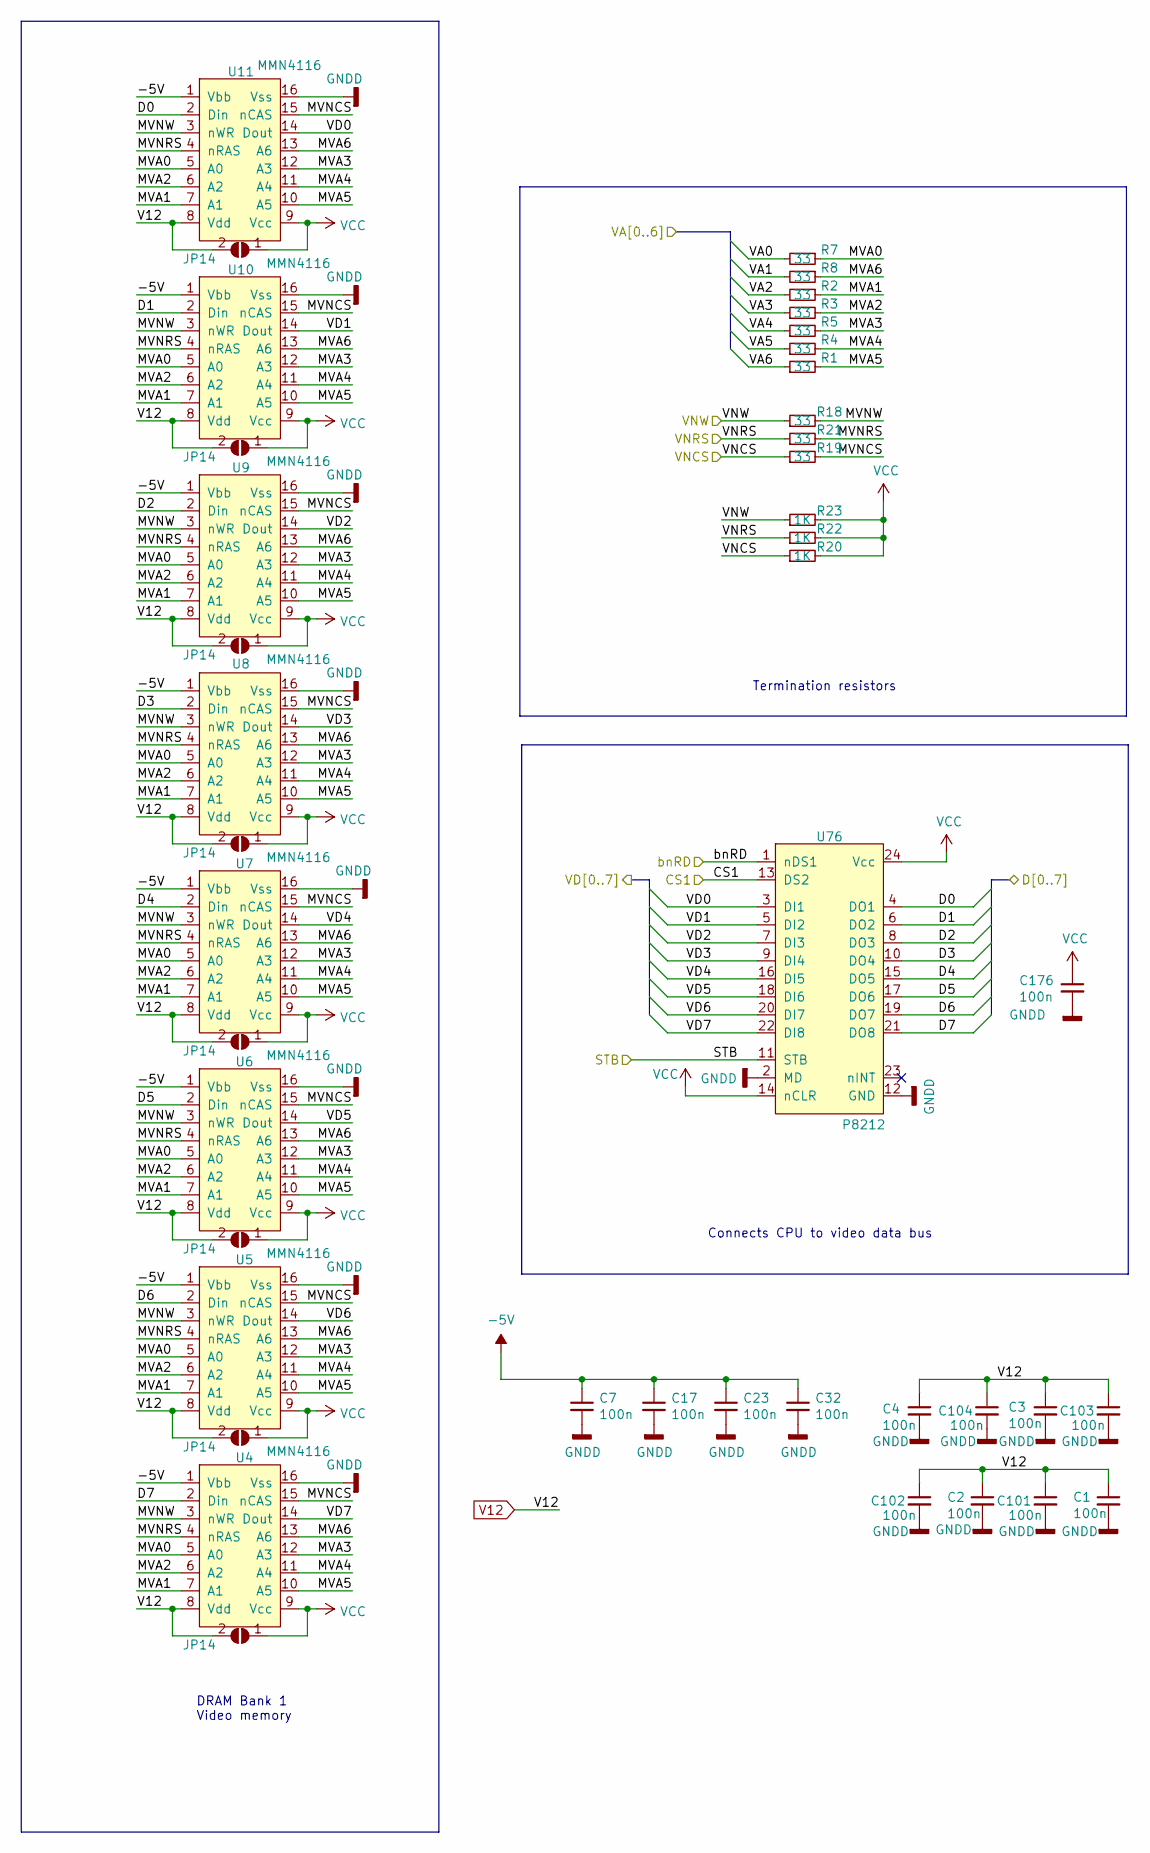
[picture p38: schematic Video_memory.kicad_sch]

Parts:
C1, C2, C3, C4, C7, C17, C23, C32, C101, C102, C103, C104: 100n; C_THT_762_254
C176: 100n; C_THT_508_254
JP14: SolderJumper_2_Open; SolderJumper-2_P1.3mm_Open_TrianglePad1.0x1.5mm
R1, R2, R3, R4, R5, R7, R8, R18, R19, R21: 33; R_Axial_DIN0204_L3.6mm_D1.6mm_P5.08mm_Horizontal
R20, R22, R23: 1K; R_Axial_DIN0204_L3.6mm_D1.6mm_P5.08mm_Horizontal
U4, U5, U6, U7, U8, U9, U10, U11: MMN4116; DIP-16_W7.62mm
U76: P8212; DIP-24_W15.24mm

Connections:
-5V: C7.1, C17.1, C23.1, C32.1, U4.1 (Vbb), U5.1 (Vbb), U6.1 (Vbb), U7.1 (Vbb), U8.1 (Vbb), U9.1 (Vbb), U10.1 (Vbb), U11.1 (Vbb)
CS1: U76.13 (DS2)
D0: U11.2 (Din), U76.4 (DO1)
D1: U10.2 (Din), U76.6 (DO2)
D2: U9.2 (Din), U76.8 (DO3)
D3: U8.2 (Din), U76.10 (DO4)
D4: U7.2 (Din), U76.15 (DO5)
D5: U6.2 (Din), U76.17 (DO6)
D6: U5.2 (Din), U76.19 (DO7)
D7: U4.2 (Din), U76.21 (DO8)
GNDD: C1.2, C2.2, C3.2, C4.2, C7.2, C17.2, C23.2, C32.2, C101.2, C102.2, C103.2, C104.2, C176.2, U4.16 (Vss), U5.16 (Vss), U6.16 (Vss), U7.16 (Vss), U8.16 (Vss), U9.16 (Vss), U10.16 (Vss), U11.16 (Vss), U76.2 (MD), U76.12 (GND)
MVA0: R7.1, U4.5 (A0), U5.5 (A0), U6.5 (A0), U7.5 (A0), U8.5 (A0), U9.5 (A0), U10.5 (A0), U11.5 (A0)
MVA1: R2.1, U4.7 (A1), U5.7 (A1), U6.7 (A1), U7.7 (A1), U8.7 (A1), U9.7 (A1), U10.7 (A1), U11.7 (A1)
MVA2: R3.2, U4.6 (A2), U5.6 (A2), U6.6 (A2), U7.6 (A2), U8.6 (A2), U9.6 (A2), U10.6 (A2), U11.6 (A2)
MVA3: R5.2, U4.12 (A3), U5.12 (A3), U6.12 (A3), U7.12 (A3), U8.12 (A3), U9.12 (A3), U10.12 (A3), U11.12 (A3)
MVA4: R4.2, U4.11 (A4), U5.11 (A4), U6.11 (A4), U7.11 (A4), U8.11 (A4), U9.11 (A4), U10.11 (A4), U11.11 (A4)
MVA5: R1.2, U4.10 (A5), U5.10 (A5), U6.10 (A5), U7.10 (A5), U8.10 (A5), U9.10 (A5), U10.10 (A5), U11.10 (A5)
MVA6: R8.1, U4.13 (A6), U5.13 (A6), U6.13 (A6), U7.13 (A6), U8.13 (A6), U9.13 (A6), U10.13 (A6), U11.13 (A6)
MVNCS: R19.2, U4.15 (nCAS), U5.15 (nCAS), U6.15 (nCAS), U7.15 (nCAS), U8.15 (nCAS), U9.15 (nCAS), U10.15 (nCAS), U11.15 (nCAS)
MVNRS: R21.2, U4.4 (nRAS), U5.4 (nRAS), U6.4 (nRAS), U7.4 (nRAS), U8.4 (nRAS), U9.4 (nRAS), U10.4 (nRAS), U11.4 (nRAS)
MVNW: R18.2, U4.3 (nWR), U5.3 (nWR), U6.3 (nWR), U7.3 (nWR), U8.3 (nWR), U9.3 (nWR), U10.3 (nWR), U11.3 (nWR)
STB: U76.11 (STB)
V12: C1.1, C2.1, C3.1, C4.1, C101.1, C102.1, C103.1, C104.1, JP14.2 (B), U4.8 (Vdd), U5.8 (Vdd), U6.8 (Vdd), U7.8 (Vdd), U8.8 (Vdd), U9.8 (Vdd), U10.8 (Vdd), U11.8 (Vdd)
VA0: R7.2
VA1: R8.2
VA2: R2.2
VA3: R3.1
VA4: R5.1
VA5: R4.1
VA6: R1.1
VCC: C176.1, JP14.1 (A), R20.2, R22.2, R23.2, U4.9 (Vcc), U5.9 (Vcc), U6.9 (Vcc), U7.9 (Vcc), U8.9 (Vcc), U9.9 (Vcc), U10.9 (Vcc), U11.9 (Vcc), U76.14 (nCLR), U76.24 (Vcc)
VD0: U11.14 (Dout), U76.3 (DI1)
VD1: U10.14 (Dout), U76.5 (DI2)
VD2: U9.14 (Dout), U76.7 (DI3)
VD3: U8.14 (Dout), U76.9 (DI4)
VD4: U7.14 (Dout), U76.16 (DI5)
VD5: U6.14 (Dout), U76.18 (DI6)
VD6: U5.14 (Dout), U76.20 (DI7)
VD7: U4.14 (Dout), U76.22 (DI8)
VNCS: R19.1, R20.1
VNRS: R21.1, R22.1
VNW: R18.1, R23.1
bnRD: U76.1 (nDS1)

Notes on the sheet:
Connects CPU to video data bus
DRAM Bank 1 Video memory
Termination resistors
