ceteras/CoBra/mainboard/2layer/kicad/Z80_CPU.kicad_sch

## KiCad design mainboard/2layer/kicad/Z80_CPU.kicad_sch (2023-11-29)

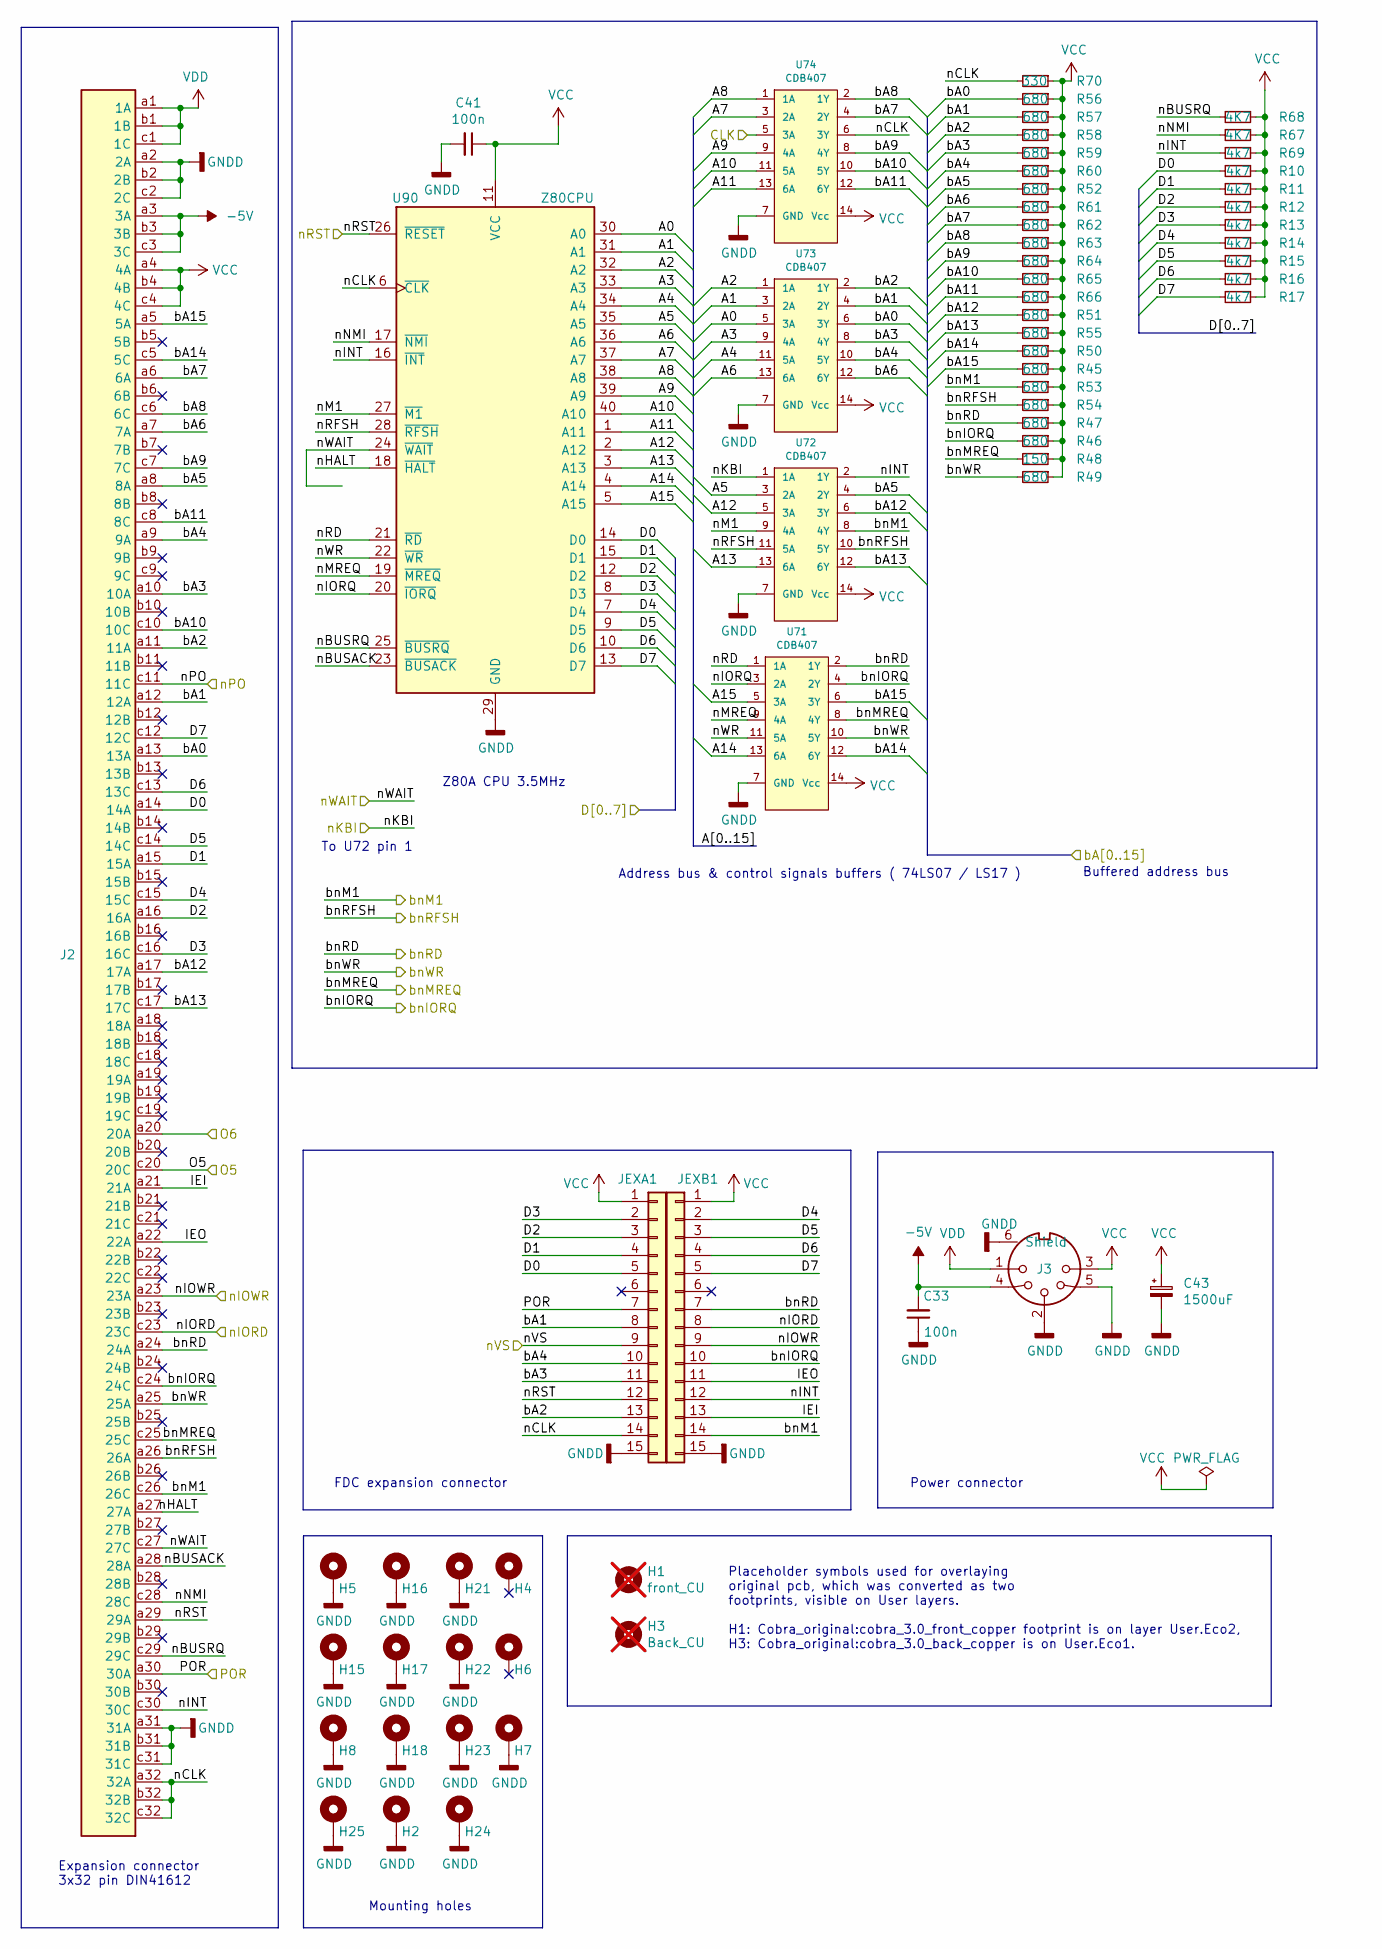
[picture p39: schematic Z80_CPU.kicad_sch]

Parts:
C33, C41: 100n; C_THT_508_254
C43: 1500uF; CP_Axial_L25.0mm_D9.0mm_P30.00mm_Horizontal
H1: front_CU; cobra_3.0_front_copper; not fitted
H2, H4, H5, H6, H8, H15, H16, H17, H18, H21, H22, H24, H25: MountingHole_Pad; MountingHole_2.5mm_Pad
H3: Back_CU; cobra_3.0_back_copper; not fitted
H7, H23: e; MountingHole_2.5mm_Pad
J2: C96ABC; DIN41612_R_3x32_Male_Horizontal_THT
J3: DIN-5
JEXA1: Conn_01x15; PinHeader_1x15_P2.54mm_Vertical
JEXB1: Conn_01x15; PinHeader_1x15_P2.54mm_Vertical
R10, R11, R12, R13, R14, R15, R16, R17, R69: 4k7; R_Axial_DIN0204_L3.6mm_D1.6mm_P5.08mm_Horizontal
R45, R46, R47, R49, R50, R51, R52, R53, R54, R55, R56, R57, R58, R59, R60, R61, R62, R63, R64, R65, R66: 680; R_Axial_DIN0204_L3.6mm_D1.6mm_P5.08mm_Horizontal
R48: 150; R_Axial_DIN0204_L3.6mm_D1.6mm_P5.08mm_Horizontal
R67, R68: 4K7; R_Axial_DIN0204_L3.6mm_D1.6mm_P5.08mm_Horizontal
R70: 330; R_Axial_DIN0204_L3.6mm_D1.6mm_P5.08mm_Horizontal
U71, U72, U73, U74: CDB407; DIP-14_W7.62mm
U90: Z80CPU; DIP-40_W15.24mm

Connections:
-5V: C33.2, J2.a3 (3A), J2.b3 (3B), J2.c3 (3C), J3.4
A0: U73.5 (3A), U90.30 (A0)
A1: U73.3 (2A), U90.31 (A1)
A2: U73.1 (1A), U90.32 (A2)
A3: U73.9 (4A), U90.33 (A3)
A4: U73.11 (5A), U90.34 (A4)
A5: U72.3 (2A), U90.35 (A5)
A6: U73.13 (6A), U90.36 (A6)
A7: U74.3 (2A), U90.37 (A7)
A8: U74.1 (1A), U90.38 (A8)
A9: U74.9 (4A), U90.39 (A9)
A10: U74.11 (5A), U90.40 (A10)
A11: U74.13 (6A), U90.1 (A11)
A12: U72.5 (3A), U90.2 (A12)
A13: U72.13 (6A), U90.3 (A13)
A14: U71.13 (6A), U90.4 (A14)
A15: U71.5 (3A), U90.5 (A15)
CLK: U74.5 (3A)
D0: J2.a14 (14A), JEXA1.5, R10.2, U90.14 (D0)
D1: J2.a15 (15A), JEXA1.4, R11.2, U90.15 (D1)
D2: J2.a16 (16A), JEXA1.3, R12.2, U90.12 (D2)
D3: J2.c16 (16C), JEXA1.2, R13.2, U90.8 (D3)
D4: J2.c15 (15C), JEXB1.2, R14.2, U90.7 (D4)
D5: J2.c14 (14C), JEXB1.3, R15.2, U90.9 (D5)
D6: J2.c13 (13C), JEXB1.4, R16.2, U90.10 (D6)
D7: J2.c12 (12C), JEXB1.5, R17.2, U90.13 (D7)
GNDD: C33.1, C41.2, C43.2, H2.1, H5.1, H7.1, H8.1, H15.1, H16.1, H17.1, H18.1, H21.1, H22.1, H23.1, H24.1, H25.1, J2.a2 (2A), J2.a31 (31A), J2.b2 (2B), J2.b31 (31B), J2.c2 (2C), J2.c31 (31C), J3.2, J3.5, J3.6 (Shield), JEXA1.15, JEXB1.15, U71.7 (GND), U72.7 (GND), U73.7 (GND), U74.7 (GND), U90.29 (GND)
IEI: J2.a21 (21A), JEXB1.13
IEO: J2.a22 (22A), JEXB1.11
O5: J2.c20 (20C)
O6: J2.a20 (20A)
POR: J2.a30 (30A), JEXA1.7
VCC: C41.1, C43.1, J2.a4 (4A), J2.b4 (4B), J2.c4 (4C), J3.3, JEXA1.1, JEXB1.1, R10.1, R11.1, R12.1, R13.1, R14.1, R15.1, R16.1, R17.1, R45.1, R46.1, R47.1, R48.1, R49.1, R50.1, R51.1, R52.1, R53.1, R54.1, R55.1, R56.1, R57.1, R58.1, R59.1, R60.1, R61.1, R62.1, R63.1, R64.1, R65.1, R66.1, R67.1, R68.1, R69.1, R70.1, U71.14 (Vcc), U72.14 (Vcc), U73.14 (Vcc), U74.14 (Vcc), U90.11 (VCC)
VDD: J2.a1 (1A), J2.b1 (1B), J2.c1 (1C), J3.1
bA0: J2.a13 (13A), R56.2, U73.6 (3Y)
bA1: J2.a12 (12A), JEXA1.8, R57.2, U73.4 (2Y)
bA2: J2.a11 (11A), JEXA1.13, R58.2, U73.2 (1Y)
bA3: J2.a10 (10A), JEXA1.11, R59.2, U73.8 (4Y)
bA4: J2.a9 (9A), JEXA1.10, R60.2, U73.10 (5Y)
bA5: J2.a8 (8A), R52.2, U72.4 (2Y)
bA6: J2.a7 (7A), R61.2, U73.12 (6Y)
bA7: J2.a6 (6A), R62.2, U74.4 (2Y)
bA8: J2.c6 (6C), R63.2, U74.2 (1Y)
bA9: J2.c7 (7C), R64.2, U74.8 (4Y)
bA10: J2.c10 (10C), R65.2, U74.10 (5Y)
bA11: J2.c8 (8C), R66.2, U74.12 (6Y)
bA12: J2.a17 (17A), R51.2, U72.6 (3Y)
bA13: J2.c17 (17C), R55.2, U72.12 (6Y)
bA14: J2.c5 (5C), R50.2, U71.12 (6Y)
bA15: J2.a5 (5A), R45.2, U71.6 (3Y)
bnIORQ: J2.c24 (24C), JEXB1.10, R46.2, U71.4 (2Y)
bnM1: J2.c26 (26C), JEXB1.14, R53.2, U72.8 (4Y)
bnMREQ: J2.c25 (25C), R48.2, U71.8 (4Y)
bnRD: J2.a24 (24A), JEXB1.7, R47.2, U71.2 (1Y)
bnRFSH: J2.a26 (26A), R54.2, U72.10 (5Y)
bnWR: J2.a25 (25A), R49.2, U71.10 (5Y)
nBUSACK: J2.a28 (28A), U90.23 (~BUSACK)
nBUSRQ: J2.c29 (29C), R68.2, U90.25 (~BUSRQ)
nCLK: J2.a32 (32A), J2.b32 (32B), J2.c32 (32C), JEXA1.14, R70.2, U74.6 (3Y), U90.6 (~CLK)
nHALT: J2.a27 (27A), U90.18 (~HALT)
nINT: J2.c30 (30C), JEXB1.12, R69.2, U72.2 (1Y), U90.16 (~INT)
nIORD: J2.c23 (23C), JEXB1.8
nIORQ: U71.3 (2A), U90.20 (~IORQ)
nIOWR: J2.a23 (23A), JEXB1.9
nKBI: U72.1 (1A)
nM1: U72.9 (4A), U90.27 (~M1)
nMREQ: U71.9 (4A), U90.19 (~MREQ)
nNMI: J2.c28 (28C), R67.2, U90.17 (~NMI)
nPO: J2.c11 (11C)
nRD: U71.1 (1A), U90.21 (~RD)
nRFSH: U72.11 (5A), U90.28 (~RFSH)
nRST: J2.a29 (29A), JEXA1.12, U90.26 (~RESET)
nVS: JEXA1.9
nWAIT: J2.c27 (27C), U90.24 (~WAIT)
nWR: U71.11 (5A), U90.22 (~WR)

Notes on the sheet:
Expansion connector 3x32 pin DIN41612
Address bus & control signals buffers ( 74LS07 / LS17 )
To U72 pin 1
FDC expansion connector
Placeholder symbols used for overlaying original pcb, which was converted as two footprints, visible on User layers. H1: Cobra_original:cobra_3.0_front_copper footprint is on layer User.Eco2, H3: Cobra_original:cobra_3.0_back_copper is on User.Eco1.
Power connector
Buffered address bus
Mounting holes
Z80A CPU 3.5MHz
