ceteras/CoBra/mainboard/2layer/kicad/config_selection.kicad_sch

## KiCad design mainboard/2layer/kicad/config_selection.kicad_sch (2023-11-16)

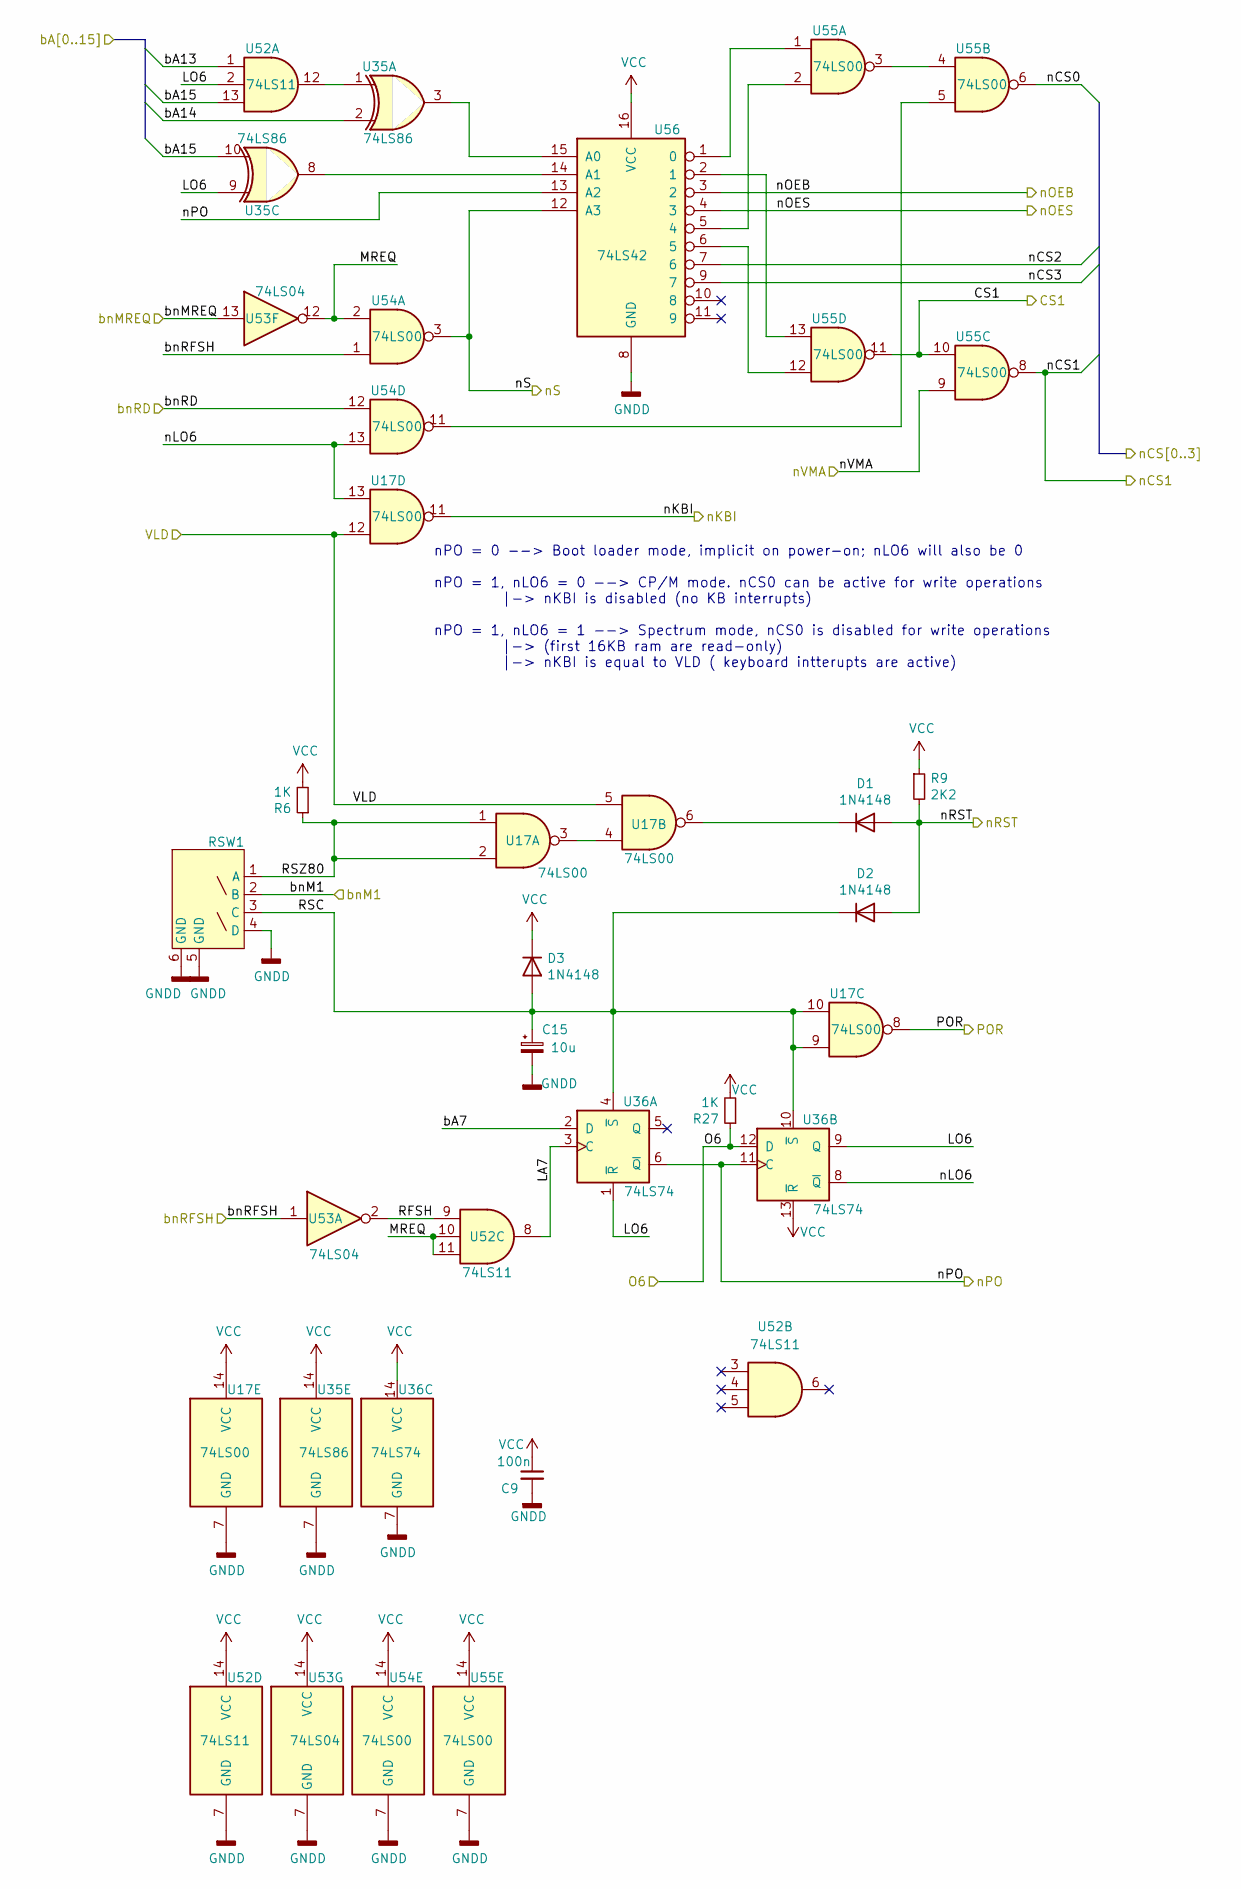
[picture p40: schematic config_selection.kicad_sch]

Parts:
C9: 100n; C_THT_508_254
C15: 10u; C_THT_508_254
D1, D2, D3: 1N4148; D_DO-35_SOD27_P7.62mm_Horizontal
R6, R27: 1K; R_Axial_DIN0204_L3.6mm_D1.6mm_P5.08mm_Horizontal
R9: 2K2; R_Axial_DIN0204_L3.6mm_D1.6mm_P5.08mm_Horizontal
RSW1: Reset_Switch
U17, U54, U55: 74LS00; DIP-14_W7.62mm
U35: 74LS86; DIP-14_W7.62mm
U36: 74LS74; DIP-14_W7.62mm
U52: 74LS11; DIP-14_W7.62mm
U53: 74LS04; DIP-14_W7.62mm
U56: 74LS42; DIP-16_W7.62mm

Connections:
CS1: U55.10, U55.11
GNDD: C9.2, C15.2, RSW1.4 (D), RSW1.5 (GND), RSW1.6 (GND), U17.7 (GND), U35.7 (GND), U36.7 (GND), U52.7 (GND), U53.7 (GND), U54.7 (GND), U55.7 (GND), U56.8 (GND)
LA7: U36.3 (C), U52.8
LO6: U35.9, U36.1 (~R), U36.9 (Q), U52.2
MREQ: U52.10, U52.11, U53.12, U54.2
unnamed: D1.1 (K), U17.6
unnamed: U17.3, U17.4
unnamed: U35.1, U52.12
unnamed: U35.3, U56.15 (A0)
unnamed: U35.8, U56.14 (A1)
unnamed: U54.11, U55.5
unnamed: U55.1, U56.1 (0)
unnamed: U55.2, U56.5 (4)
unnamed: U55.3, U55.4
unnamed: U55.12, U56.6 (5)
unnamed: U55.13, U56.2 (1)
O6: R27.1, U36.12 (D)
POR: U17.8
RFSH: U52.9, U53.2
RSC: C15.1, D2.1 (K), D3.2 (A), RSW1.3 (C), U17.9, U17.10, U36.4 (~S), U36.10 (~S)
RSZ80: R6.1, RSW1.1 (A), U17.1, U17.2
VCC: C9.1, D3.1 (K), R6.2, R9.1, R27.2, U17.14 (VCC), U35.14 (VCC), U36.13 (~R), U36.14 (VCC), U52.14 (VCC), U53.14 (VCC), U54.14 (VCC), U55.14 (VCC), U56.16 (VCC)
VLD: U17.5, U17.12
bA7: U36.2 (D)
bA13: U52.1
bA14: U35.2
bA15: U35.10, U52.13
bnM1: RSW1.2 (B)
bnMREQ: U53.13
bnRD: U54.12
bnRFSH: U53.1, U54.1
nCS0: U55.6
nCS1: U55.8
nCS2: U56.7 (6)
nCS3: U56.9 (7)
nKBI: U17.11
nLO6: U17.13, U36.8 (~Q), U54.13
nOEB: U56.3 (2)
nOES: U56.4 (3)
nPO: U36.6 (~Q), U36.11 (C), U56.13 (A2)
nRST: D1.2 (A), D2.2 (A), R9.2
nS: U54.3, U56.12 (A3)
nVMA: U55.9

Notes on the sheet:
nPO = 0 --> Boot loader mode, implicit on power-on; nLO6 will also be 0 nPO = 1, nLO6 = 0 --> CP/M mode. nCS0 can be active for write operations |-> nKBI is disabled (no KB interrupts) nPO = 1, nLO6 = 1 --> Spectrum mode, nCS0 is disabled for write operations |-> (first 16KB ram are read-only) |-> 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
