ceteras/CoBra/mainboard/2layer/kicad/monitor.kicad_sch

## KiCad design mainboard/2layer/kicad/monitor.kicad_sch (2023-11-15)

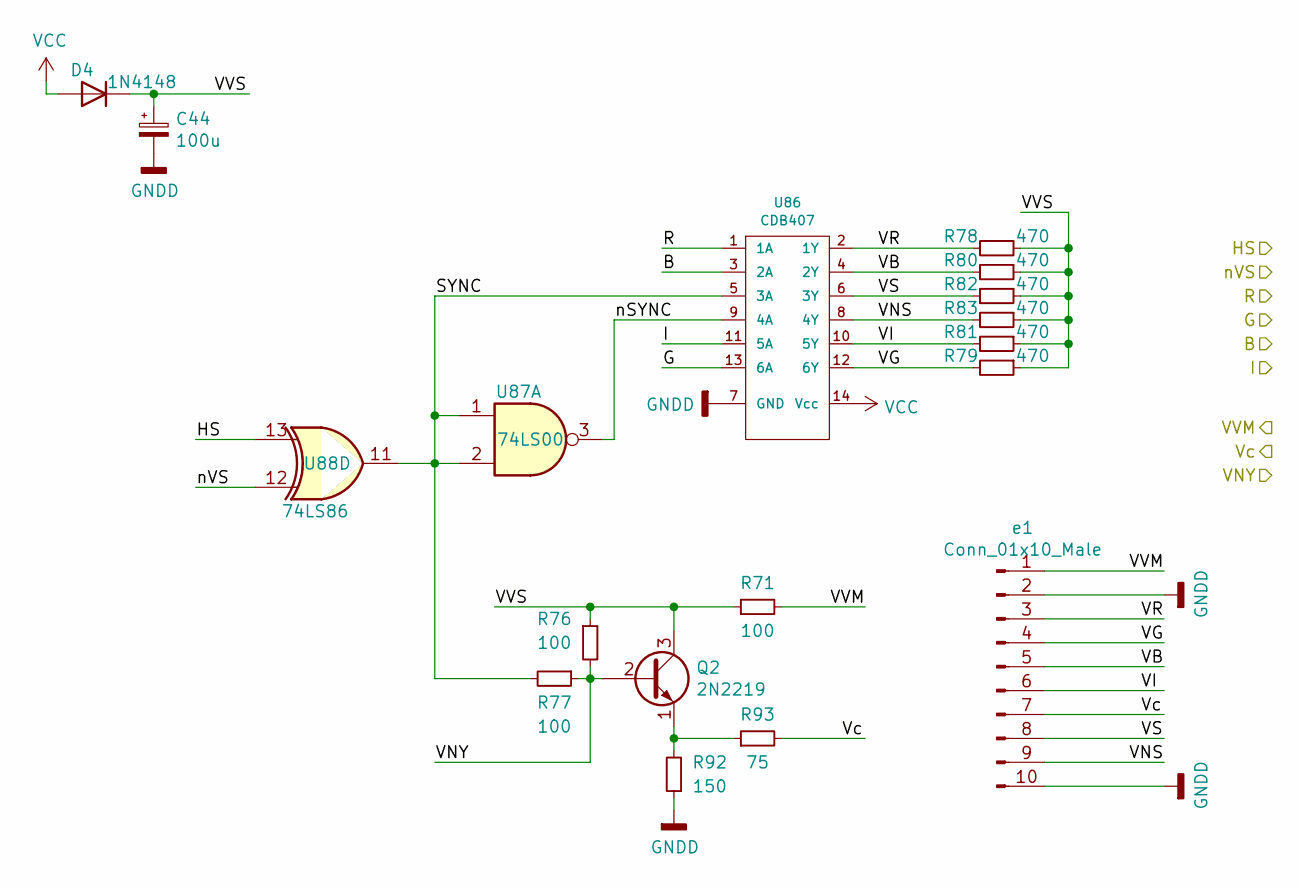
[picture p41: schematic monitor.kicad_sch]

Parts:
C44: 100u; C_Rect_L7.0mm_W2.0mm_P5.00mm
D4: 1N4148; D_DO-35_SOD27_P7.62mm_Horizontal
Q2: 2N2219; TO-92-Cobra
R71, R76, R77: 100; R_Axial_DIN0204_L3.6mm_D1.6mm_P5.08mm_Horizontal
R78, R79, R80, R81, R82, R83: 470; R_Axial_DIN0204_L3.6mm_D1.6mm_P5.08mm_Horizontal
R92: 150; R_Axial_DIN0204_L3.6mm_D1.6mm_P5.08mm_Horizontal
R93: 75; R_Axial_DIN0204_L3.6mm_D1.6mm_P5.08mm_Horizontal
U86: CDB407; DIP-14_W7.62mm
U87: 74LS00; DIP-14_W7.62mm
U88: 74LS86; DIP-14_W7.62mm
e1: Conn_01x10_Male; PinHeader_1x10_P2.54mm_Vertical

Connections:
B: U86.3 (2A)
G: U86.13 (6A)
GNDD: C44.2, R92.1, U86.7 (GND), e1.2, e1.10
HS: U88.13
I: U86.11 (5A)
unnamed: Q2.1 (E), R92.2, R93.1
R: U86.1 (1A)
SYNC: R77.2, U86.5 (3A), U87.1, U87.2, U88.11
VB: R80.2, U86.4 (2Y), e1.5
VCC: D4.2 (A), U86.14 (Vcc)
VG: R79.2, U86.12 (6Y), e1.4
VI: R81.2, U86.10 (5Y), e1.6
VNS: R83.2, U86.8 (4Y), e1.9
VNY: Q2.2 (B), R76.2, R77.1
VR: R78.2, U86.2 (1Y), e1.3
VS: R82.2, U86.6 (3Y), e1.8
VVM: R71.2, e1.1
VVS: C44.1, D4.1 (K), Q2.3 (C), R71.1, R76.1, R78.1, R79.1, R80.1, R81.1, R82.1, R83.1
Vc: R93.2, e1.7
nSYNC: U86.9 (4A), U87.3
nVS: U88.12
