ceteras/CoBra/mainboard/2layer/kicad/video_generator.kicad_sch

## KiCad design mainboard/2layer/kicad/video_generator.kicad_sch (2023-11-16)

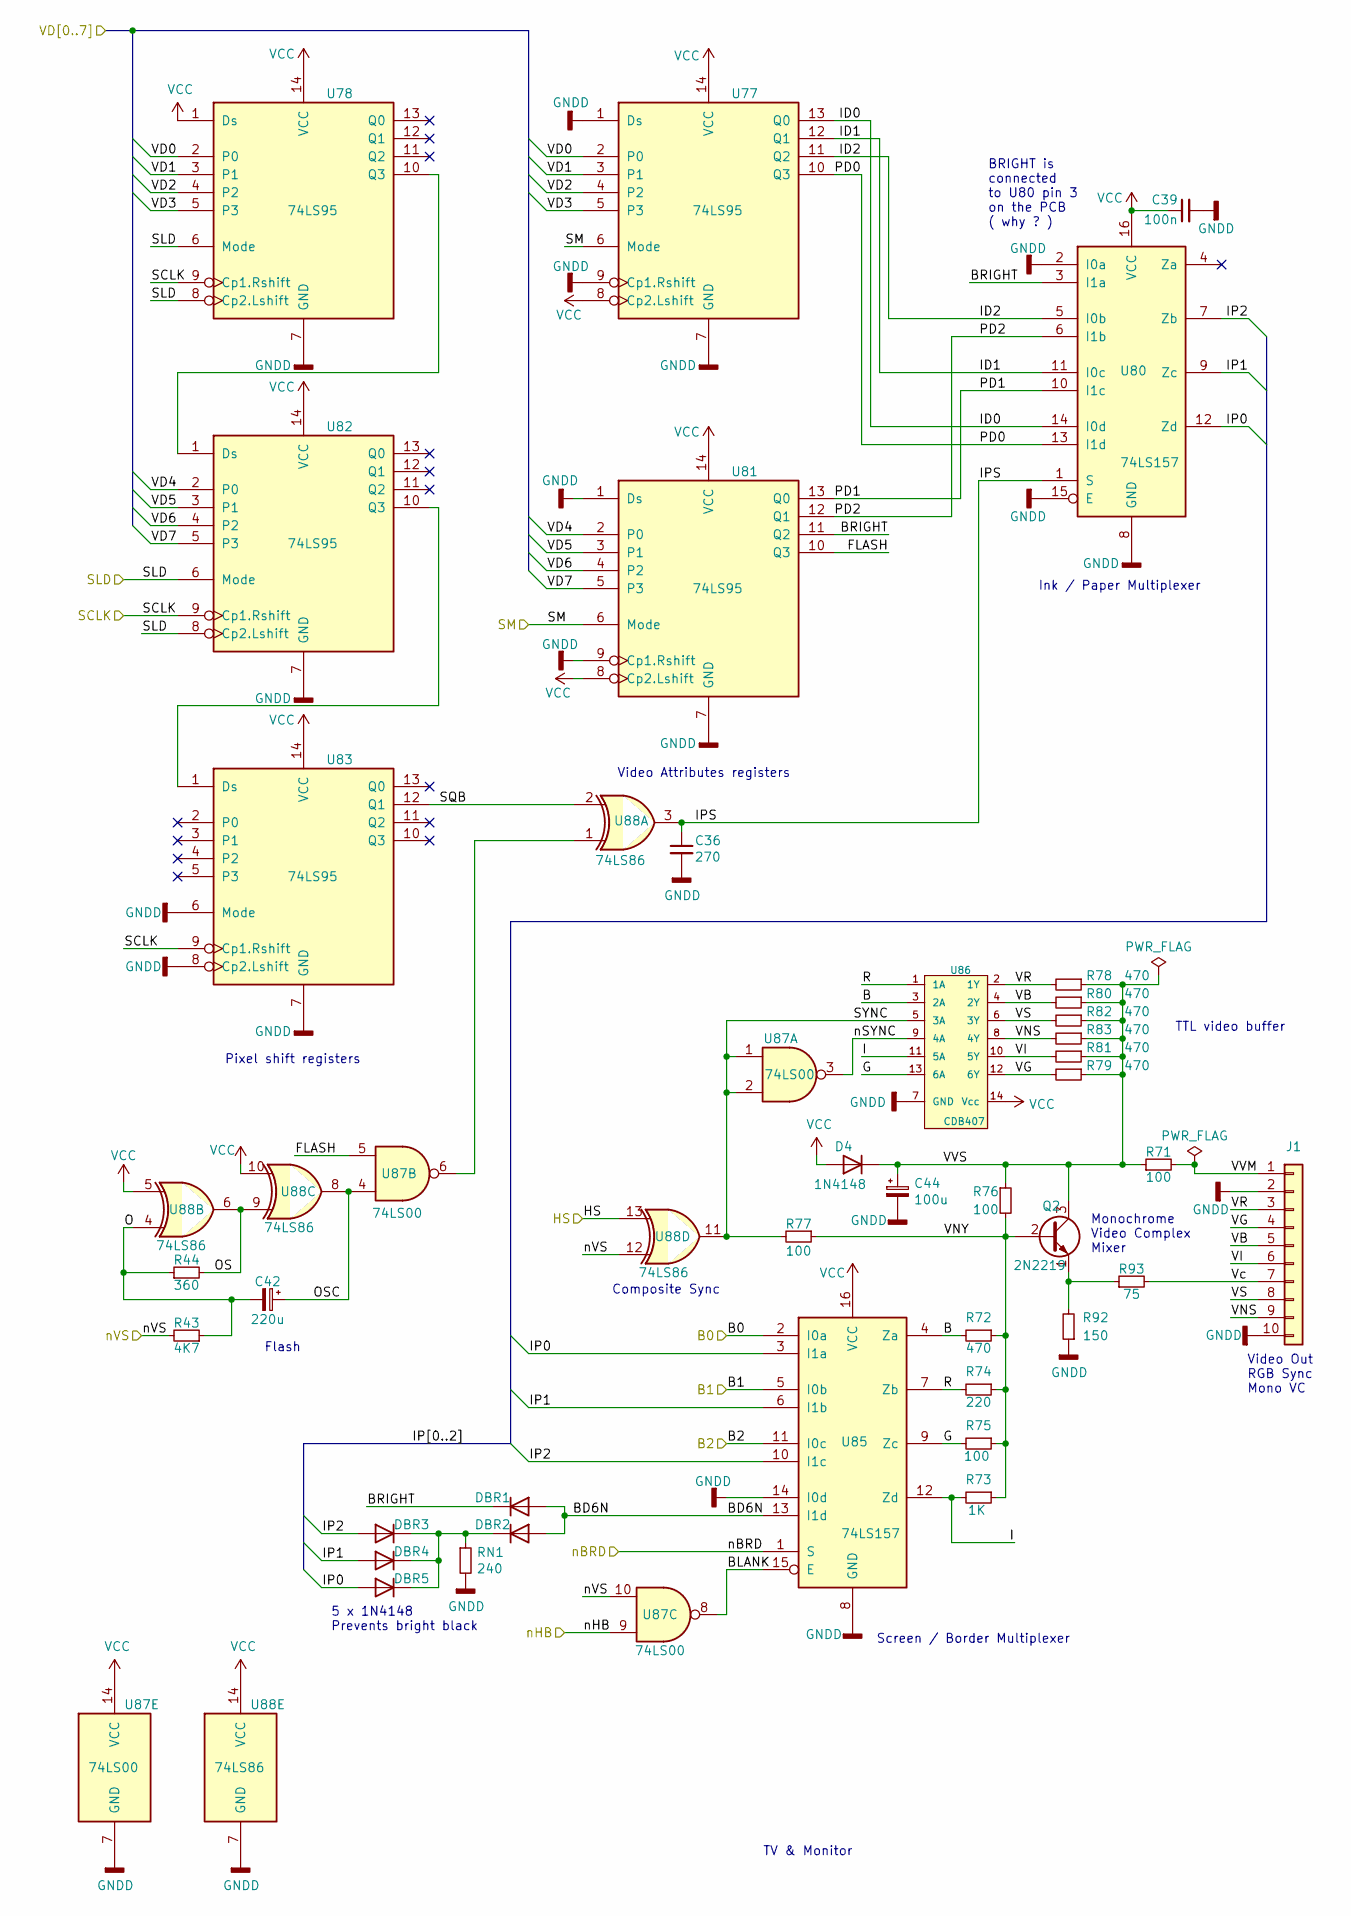
[picture p42: schematic video_generator.kicad_sch]

Parts:
C36: 270; C_THT_762_254
C39: 100n; C_THT_508_254
C42: 220u; CP_Radial_D8.0mm_P5.00mm
C44: 100u; C_THT_508_254
D4: 1N4148; D_DO-35_SOD27_P7.62mm_Horizontal
DBR1, DBR2, DBR3, DBR4, DBR5: 1N4148; D_DO-35_SOD27_P7.62mm_Horizontal
J1: Conn_01x10; PinHeader_1x10_P2.54mm_Vertical
Q2: 2N2219; TO-92-Cobra
R43: 4K7; R_Axial_DIN0204_L3.6mm_D1.6mm_P5.08mm_Horizontal
R44: 360; R_Axial_DIN0204_L3.6mm_D1.6mm_P5.08mm_Horizontal
R71, R75, R76, R77: 100; R_Axial_DIN0204_L3.6mm_D1.6mm_P5.08mm_Horizontal
R72, R78, R79, R80, R81, R82, R83: 470; R_Axial_DIN0204_L3.6mm_D1.6mm_P5.08mm_Horizontal
R73: 1K; R_Axial_DIN0204_L3.6mm_D1.6mm_P5.08mm_Horizontal
R74: 220; R_Axial_DIN0204_L3.6mm_D1.6mm_P5.08mm_Horizontal
R92: 150; R_Axial_DIN0204_L3.6mm_D1.6mm_P5.08mm_Horizontal
R93: 75; R_Axial_DIN0204_L3.6mm_D1.6mm_P5.08mm_Horizontal
RN1: 240; R_Axial_DIN0204_L3.6mm_D1.6mm_P5.08mm_Horizontal
U77, U78, U81, U82, U83: 74LS95; DIP-14_W7.62mm
U80, U85: 74LS157; DIP-16_W7.62mm
U86: CDB407; DIP-14_W7.62mm
U87: 74LS00; DIP-14_W7.62mm
U88: 74LS86; DIP-14_W7.62mm

Connections:
B: R72.2, U85.4 (Za), U86.3 (2A)
B0: U85.2 (I0a)
B1: U85.5 (I0b)
B2: U85.11 (I0c)
BD6N: DBR1.2 (A), DBR2.2 (A), U85.13 (I1d)
BLANK: U85.15 (E), U87.8
BRIGHT: DBR1.1 (K), U80.3 (I1a), U81.11 (Q2)
FLASH: U81.10 (Q3), U87.5
G: R75.2, U85.9 (Zc), U86.13 (6A)
GNDD: C36.2, C39.2, C44.2, J1.2, J1.10, R92.1, RN1.2, U77.1 (Ds), U77.7 (GND), U77.9 (Cp1.Rshift), U78.7 (GND), U80.2 (I0a), U80.8 (GND), U80.15 (E), U81.1 (Ds), U81.7 (GND), U81.9 (Cp1.Rshift), U82.7 (GND), U83.6 (Mode), U83.7 (GND), U83.8 (Cp2.Lshift), U85.8 (GND), U85.14 (I0d), U86.7 (GND), U87.7 (GND), U88.7 (GND)
HS: U88.13
I: R73.2, U85.12 (Zd), U86.11 (5A)
ID0: U77.13 (Q0), U80.14 (I0d)
ID1: U77.12 (Q1), U80.11 (I0c)
ID2: U77.11 (Q2), U80.5 (I0b)
IP0: DBR5.2 (A), U80.12 (Zd), U85.3 (I1a)
IP1: DBR4.2 (A), U80.9 (Zc), U85.6 (I1b)
IP2: DBR3.2 (A), U80.7 (Zb), U85.10 (I1c)
IPS: C36.1, U80.1 (S), U88.3
unnamed: DBR2.1 (K), DBR3.1 (K), DBR4.1 (K), DBR5.1 (K), RN1.1
unnamed: Q2.1 (E), R92.2, R93.1
unnamed: U78.10 (Q3), U82.1 (Ds)
unnamed: U82.10 (Q3), U83.1 (Ds)
unnamed: U87.6, U88.1
O: C42.2, R43.1, R44.1, U88.4
OS: R44.2, U88.6, U88.9
OSC: C42.1, U87.4, U88.8
PD0: U77.10 (Q3), U80.13 (I1d)
PD1: U80.10 (I1c), U81.13 (Q0)
PD2: U80.6 (I1b), U81.12 (Q1)
R: R74.2, U85.7 (Zb), U86.1 (1A)
SCLK: U78.9 (Cp1.Rshift), U82.9 (Cp1.Rshift), U83.9 (Cp1.Rshift)
SLD: U78.6 (Mode), U78.8 (Cp2.Lshift), U82.6 (Mode), U82.8 (Cp2.Lshift)
SM: U77.6 (Mode), U81.6 (Mode)
SQB: U83.12 (Q1), U88.2
SYNC: R77.2, U86.5 (3A), U87.1, U87.2, U88.11
VB: J1.5, R80.2, U86.4 (2Y)
VCC: C39.1, D4.2 (A), U77.8 (Cp2.Lshift), U77.14 (VCC), U78.1 (Ds), U78.14 (VCC), U80.16 (VCC), U81.8 (Cp2.Lshift), U81.14 (VCC), U82.14 (VCC), U83.14 (VCC), U85.16 (VCC), U86.14 (Vcc), U87.14 (VCC), U88.5, U88.10, U88.14 (VCC)
VD0: U77.2 (P0), U78.2 (P0)
VD1: U77.3 (P1), U78.3 (P1)
VD2: U77.4 (P2), U78.4 (P2)
VD3: U77.5 (P3), U78.5 (P3)
VD4: U81.2 (P0), U82.2 (P0)
VD5: U81.3 (P1), U82.3 (P1)
VD6: U81.4 (P2), U82.4 (P2)
VD7: U81.5 (P3), U82.5 (P3)
VG: J1.4, R79.2, U86.12 (6Y)
VI: J1.6, R81.2, U86.10 (5Y)
VNS: J1.9, R83.2, U86.8 (4Y)
VNY: Q2.2 (B), R72.1, R73.1, R74.1, R75.1, R76.2, R77.1
VR: J1.3, R78.2, U86.2 (1Y)
VS: J1.8, R82.2, U86.6 (3Y)
VVM: J1.1, R71.2
VVS: C44.1, D4.1 (K), Q2.3 (C), R71.1, R76.1, R78.1, R79.1, R80.1, R81.1, R82.1, R83.1
Vc: J1.7, R93.2
nBRD: U85.1 (S)
nHB: U87.9
nSYNC: U86.9 (4A), U87.3
nVS: R43.2, U87.10, U88.12

Notes on the sheet:
Monochrome Video Complex Mixer
Video Out RGB Sync Mono VC
Screen / Border Multiplexer
TV & Monitor
Pixel shift registers
5 x 1N4148 Prevents bright black
TTL video buffer
Flash
Video Attributes registers
BRIGHT is connected to U80 pin 3 on the PCB ( why ? )
Composite Sync
Ink / Paper Multiplexer
